z2010012286/Robot_car/models_v2/X3PI_3D_20220615175044.step

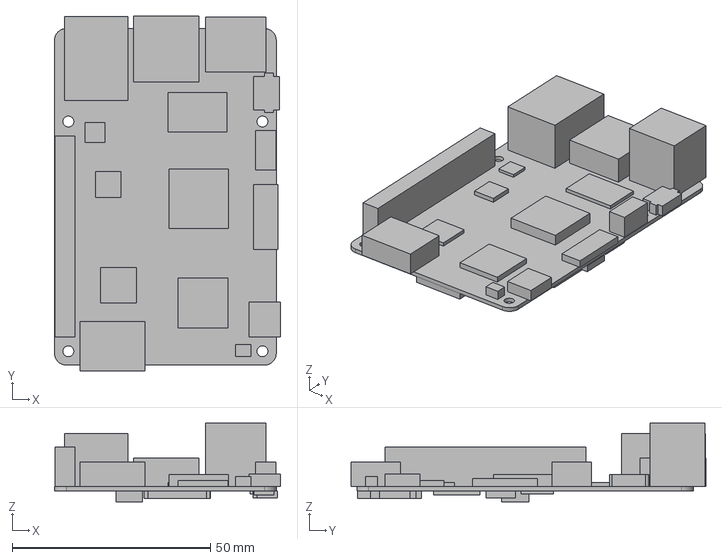
[picture p12: CAD file, 2022-10-31]
models_v2/X3PI_3D_20220615175044.step
57.1 x 89.6 x 19.9 mm
