z2010012286/Robot_car/models_v2/motor.SLDPRT

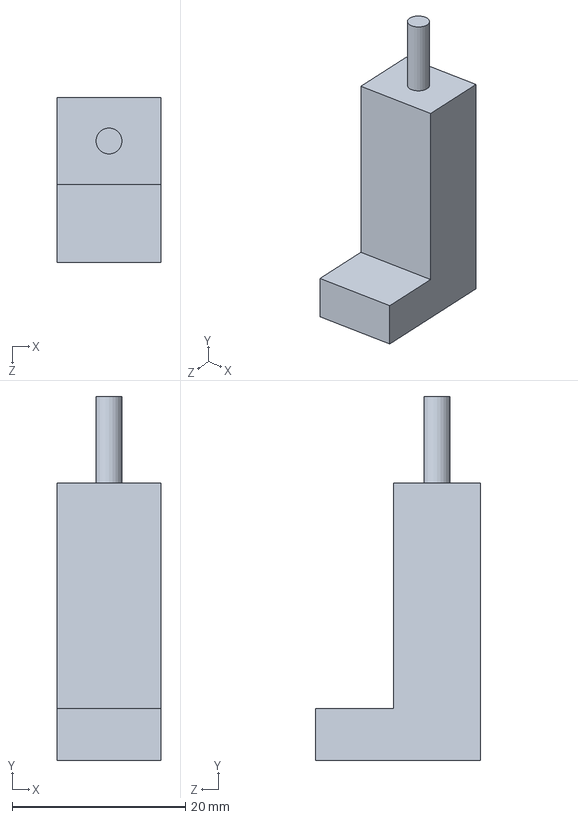
[picture p13: CAD file, 2022-10-31]
models_v2/motor.SLDPRT
12.0 x 42.0 x 19.0 mm
