z2010012286/Robot_car/models_v2/battery.SLDPRT

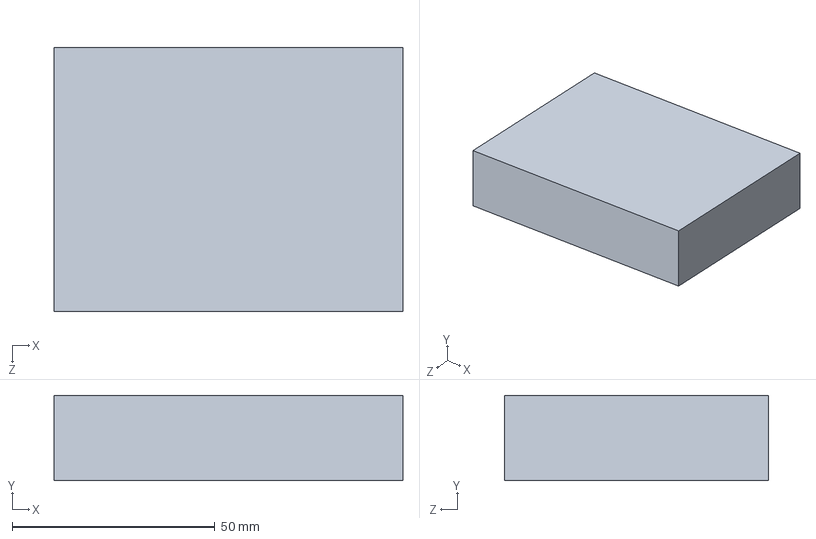
[picture p14: CAD file, 2022-10-31]
models_v2/battery.SLDPRT
86.0 x 21.0 x 65.0 mm
