z2010012286/Robot_car/codes/reconfig_code/unit_test/unit_test_micro_ros/test/micro_ros_debug.txt

[1669990941.373159] debug    | SerialAgentLinux.cpp | recv_message             | [==>> SER <<==]        | client_key: 0x3D3296CC, len: 20, data: 
0000: 81 01 0F 00 03 01 04 00 00 24 00 05 03 01 04 00 00 25 00 03
[1669990941.373207] debug    | ProxyClient.cpp    | delete_object_unlock     | object deleted         | client_key: 0x3D3296CC, object_id: 0x0000
[1669990941.373290] debug    | SerialAgentLinux.cpp | send_message             | [** <<SER>> **]        | client_key: 0x3D3296CC, len: 14, data: 
0000: 81 01 00 00 05 01 06 00 00 23 00 02 00 00
[1669990941.373598] debug    | ProxyClient.cpp    | delete_object_unlock     | object deleted         | client_key: 0x3D3296CC, object_id: 0x0000
[1669990941.373628] debug    | ProxyClient.cpp    | delete_object_unlock     | object deleted         | client_key: 0x3D3296CC, object_id: 0x0000
[1669990941.373599] debug    | SerialAgentLinux.cpp | recv_message             | [==>> SER <<==]        | client_key: 0x3D3296CC, len: 12, data: 
0000: 81 01 10 00 03 01 04 00 00 26 00 12
[1669990941.373666] debug    | SerialAgentLinux.cpp | recv_message             | [==>> SER <<==]        | client_key: 0x3D3296CC, len: 20, data: 
0000: 81 01 11 00 03 01 04 00 00 27 00 15 03 01 04 00 00 28 00 13
[1669990941.373682] debug    | SerialAgentLinux.cpp | recv_message             | [==>> SER <<==]        | client_key: 0x3D3296CC, len: 24, data: 
0000: 81 01 12 00 08 01 10 00 00 29 00 06 00 00 00 01 00 00 00 00 00 00 00 00
[1669990941.373686] debug    | SerialAgentLinux.cpp | send_message             | [** <<SER>> **]        | client_key: 0x3D3296CC, len: 14, data: 
0000: 81 01 01 00 05 01 06 00 00 24 00 05 00 00
[1669990941.373757] debug    | SerialAgentLinux.cpp | send_message             | [** <<SER>> **]        | client_key: 0x3D3296CC, len: 14, data: 
0000: 81 01 02 00 05 01 06 00 00 25 00 03 00 00
[1669990941.373690] debug    | ProxyClient.cpp    | delete_object_unlock     | object deleted         | client_key: 0x3D3296CC, object_id: 0x0001
[1669990941.373817] debug    | SerialAgentLinux.cpp | send_message             | [** <<SER>> **]        | client_key: 0x3D3296CC, len: 14, data: 
0000: 81 01 03 00 05 01 06 00 00 26 00 12 00 00
[1669990941.373908] debug    | ProxyClient.cpp    | delete_object_unlock     | object deleted         | client_key: 0x3D3296CC, object_id: 0x0001
[1669990941.373926] debug    | ProxyClient.cpp    | delete_object_unlock     | object deleted         | client_key: 0x3D3296CC, object_id: 0x0001
[1669990941.373979] debug    | SerialAgentLinux.cpp | send_message             | [** <<SER>> **]        | client_key: 0x3D3296CC, len: 14, data: 
0000: 81 01 04 00 05 01 06 00 00 27 00 15 00 00
[1669990941.374041] debug    | SerialAgentLinux.cpp | send_message             | [** <<SER>> **]        | client_key: 0x3D3296CC, len: 14, data: 
0000: 81 01 05 00 05 01 06 00 00 28 00 13 00 00
[1669990941.374121] debug    | SerialAgentLinux.cpp | recv_message             | [==>> SER <<==]        | client_key: 0x3D3296CC, len: 12, data: 
0000: 81 01 13 00 03 01 04 00 00 2A 00 22
[1669990941.374331] debug    | SerialAgentLinux.cpp | recv_message             | [==>> SER <<==]        | client_key: 0x3D3296CC, len: 20, data: 
0000: 81 01 14 00 03 01 04 00 00 2B 00 06 03 01 04 00 00 2C 00 04
[1669990941.374347] debug    | SerialAgentLinux.cpp | recv_message             | [==>> SER <<==]        | client_key: 0x3D3296CC, len: 12, data: 
0000: 81 01 15 00 03 01 04 00 00 2D 00 01
[1669990941.374642] debug    | SerialAgentLinux.cpp | recv_message             | [==>> SER <<==]        | client_key: 0x3D3296CC, len: 12, data: 
0000: 81 00 00 00 03 01 04 00 00 02 FF FE
[1669990941.441336] debug    | SerialAgentLinux.cpp | recv_message             | [==>> SER <<==]        | client_key: 0x3D3296CC, len: 16, data: 
0000: 80 00 00 00 02 01 08 00 00 0A FF FD 02 00 00 00
[1669990941.465860] debug    | ProxyClient.cpp    | delete_object_unlock     | object deleted         | client_key: 0x3D3296CC, object_id: 0x0002
[1669990941.465945] debug    | SerialAgentLinux.cpp | send_message             | [** <<SER>> **]        | client_key: 0x3D3296CC, len: 14, data: 
0000: 81 01 06 00 05 01 06 00 00 2A 00 22 00 00
[1669990941.566336] debug    | ProxyClient.cpp    | delete_object_unlock     | object deleted         | client_key: 0x3D3296CC, object_id: 0x0000
[1669990941.566383] debug    | ProxyClient.cpp    | delete_object_unlock     | object deleted         | client_key: 0x3D3296CC, object_id: 0x0000
[1669990941.566455] debug    | SerialAgentLinux.cpp | send_message             | [** <<SER>> **]        | client_key: 0x3D3296CC, len: 14, data: 
0000: 81 01 07 00 05 01 06 00 00 2B 00 06 00 00
[1669990941.566472] debug    | SerialAgentLinux.cpp | send_message             | [** <<SER>> **]        | client_key: 0x3D3296CC, len: 14, data: 
0000: 81 01 08 00 05 01 06 00 00 2C 00 04 00 00
[1669990941.569401] debug    | ProxyClient.cpp    | delete_object_unlock     | object deleted         | client_key: 0x3D3296CC, object_id: 0x0000
[1669990941.569477] info     | Root.cpp           | delete_client            | delete                 | client_key: 0x3D3296CC
[1669990941.569487] info     | SessionManager.hpp | destroy_session          | session closed         | client_key: 0x3D3296CC, address: 0
[1669990942.097232] info     | Root.cpp           | create_client            | create                 | client_key: 0x6A81087C, session_id: 0x81
[1669990942.097269] info     | SessionManager.hpp | establish_session        | session established    | client_key: 0x6A81087C, address: 0
[1669990942.097346] debug    | SerialAgentLinux.cpp | send_message             | [** <<SER>> **]        | client_key: 0x6A81087C, len: 19, data: 
0000: 81 00 00 00 04 01 0B 00 00 00 58 52 43 45 01 00 01 0F 00
[1669990942.101663] debug    | SerialAgentLinux.cpp | recv_message             | [==>> SER <<==]        | client_key: 0x6A81087C, len: 48, data: 
0000: 81 80 00 00 01 07 28 00 00 0A 00 01 01 03 00 00 1A 00 00 00 00 01 0D 80 12 00 00 00 74 69 61 6E
0020: 63 69 5F 72 6F 62 6F 74 5F 6E 6F 64 65 00 00 00
[1669990942.110478] info     | ProxyClient.cpp    | create_participant       | participant created    | client_key: 0x6A81087C, participant_id: 0x000(1)
[1669990942.110544] debug    | SerialAgentLinux.cpp | send_message             | [** <<SER>> **]        | client_key: 0x6A81087C, len: 14, data: 
0000: 81 80 00 00 05 01 06 00 00 0A 00 01 00 00
[1669990942.110566] debug    | SerialAgentLinux.cpp | send_message             | [** <<SER>> **]        | client_key: 0x6A81087C, len: 13, data: 
0000: 81 00 00 00 0A 01 05 00 01 00 00 00 80
[1669990942.114766] debug    | SerialAgentLinux.cpp | recv_message             | [==>> SER <<==]        | client_key: 0x6A81087C, len: 13, data: 
0000: 81 00 00 00 0A 01 05 00 01 00 00 00 80
[1669990942.118054] debug    | SerialAgentLinux.cpp | recv_message             | [==>> SER <<==]        | client_key: 0x6A81087C, len: 88, data: 
0000: 81 80 01 00 01 07 4D 00 00 0B 00 02 02 03 00 00 3F 00 00 00 13 00 00 00 72 74 2F 6F 64 6F 6D 2F
0020: 75 6E 66 69 6C 74 65 72 65 64 00 00 01 00 00 00 1F 00 00 00 6E 61 76 5F 6D 73 67 73 3A 3A 6D 73
0040: 67 3A 3A 64 64 73 5F 3A 3A 4F 64 6F 6D 65 74 72 79 5F 00 00 01 00 00 00
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
[1669990943.109060] debug    | ProxyClient.cpp    | delete_object_unlock     | object deleted         | client_key: 0x6A81087C, object_id: 0x0000
[1669990943.109068] debug    | ProxyClient.cpp    | delete_object_unlock     | object deleted         | client_key: 0x6A81087C, object_id: 0x0001
[1669990943.109170] debug    | ProxyClient.cpp    | delete_object_unlock     | object deleted         | client_key: 0x6A81087C, object_id: 0x0001
[1669990943.109190] debug    | ProxyClient.cpp    | delete_object_unlock     | object deleted         | client_key: 0x6A81087C, object_id: 0x0001
[1669990943.109276] debug    | SerialAgentLinux.cpp | send_message             | [** <<SER>> **]        | client_key: 0x6A81087C, len: 14, data: 
0000: 81 01 01 00 05 01 06 00 00 50 00 05 00 00
[1669990943.109339] debug    | SerialAgentLinux.cpp | send_message             | [** <<SER>> **]        | client_key: 0x6A81087C, len: 14, data: 
0000: 81 01 02 00 05 01 06 00 00 51 00 03 00 00
[1669990943.109343] debug    | SerialAgentLinux.cpp | send_message             | [** <<SER>> **]        | client_key: 0x6A81087C, len: 14, data: 
0000: 81 01 03 00 05 01 06 00 00 52 00 12 00 00
[1669990943.109347] debug    | SerialAgentLinux.cpp | send_message             | [** <<SER>> **]        | client_key: 0x6A81087C, len: 14, data: 
0000: 81 01 04 00 05 01 06 00 00 53 00 15 00 00
[1669990943.109351] debug    | SerialAgentLinux.cpp | send_message             | [** <<SER>> **]        | client_key: 0x6A81087C, len: 14, data: 
0000: 81 01 05 00 05 01 06 00 00 54 00 13 00 00
[1669990943.109319] debug    | SerialAgentLinux.cpp | recv_message             | [==>> SER <<==]        | client_key: 0x6A81087C, len: 20, data: 
0000: 81 01 40 00 03 01 04 00 00 57 00 06 03 01 04 00 00 58 00 04
[1669990943.109407] debug    | SerialAgentLinux.cpp | recv_message             | [==>> SER <<==]        | client_key: 0x6A81087C, len: 12, data: 
0000: 81 01 41 00 03 01 04 00 00 59 00 01
[1669990943.109419] debug    | SerialAgentLinux.cpp | recv_message             | [==>> SER <<==]        | client_key: 0x6A81087C, len: 12, data: 
0000: 81 00 00 00 03 01 04 00 00 02 FF FE
[1669990943.121271] debug    | SerialAgentLinux.cpp | recv_message             | [==>> SER <<==]        | client_key: 0x6A81087C, len: 16, data: 
0000: 80 00 00 00 02 01 08 00 00 0A FF FD 02 00 00 00
[1669990943.169467] debug    | ProxyClient.cpp    | delete_object_unlock     | object deleted         | client_key: 0x6A81087C, object_id: 0x0002
[1669990943.169548] debug    | SerialAgentLinux.cpp | send_message             | [** <<SER>> **]        | client_key: 0x6A81087C, len: 14, data: 
0000: 81 01 06 00 05 01 06 00 00 56 00 22 00 00
[1669990943.270036] debug    | ProxyClient.cpp    | delete_object_unlock     | object deleted         | client_key: 0x6A81087C, object_id: 0x0000
[1669990943.270118] debug    | ProxyClient.cpp    | delete_object_unlock     | object deleted         | client_key: 0x6A81087C, object_id: 0x0000
[1669990943.270188] debug    | SerialAgentLinux.cpp | send_message             | [** <<SER>> **]        | client_key: 0x6A81087C, len: 14, data: 
0000: 81 01 07 00 05 01 06 00 00 57 00 06 00 00
[1669990943.270210] debug    | SerialAgentLinux.cpp | send_message             | [** <<SER>> **]        | client_key: 0x6A81087C, len: 14, data: 
0000: 81 01 08 00 05 01 06 00 00 58 00 04 00 00
[1669990943.273466] debug    | ProxyClient.cpp    | delete_object_unlock     | object deleted         | client_key: 0x6A81087C, object_id: 0x0000
[1669990943.273542] info     | Root.cpp           | delete_client            | delete                 | client_key: 0x6A81087C
[1669990943.273555] info     | SessionManager.hpp | destroy_session          | session closed         | client_key: 0x6A81087C, address: 0
[1669990943.801147] info     | Root.cpp           | create_client            | create                 | client_key: 0x2B858398, session_id: 0x81
[1669990943.801186] info     | SessionManager.hpp | establish_session        | session established    | client_key: 0x2B858398, address: 0
[1669990943.801241] debug    | SerialAgentLinux.cpp | send_message             | [** <<SER>> **]        | client_key: 0x2B858398, len: 19, data: 
0000: 81 00 00 00 04 01 0B 00 00 00 58 52 43 45 01 00 01 0F 00
[1669990943.805449] debug    | SerialAgentLinux.cpp | recv_message             | [==>> SER <<==]        | client_key: 0x2B858398, len: 48, data: 
0000: 81 80 00 00 01 07 28 00 00 0A 00 01 01 03 00 00 1A 00 00 00 00 01 00 00 12 00 00 00 74 69 61 6E
0020: 63 69 5F 72 6F 62 6F 74 5F 6E 6F 64 65 00 00 00
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
[1669990944.190704] debug    | SerialAgentLinux.cpp | send_message             | [** <<SER>> **]        | client_key: 0x2B858398, len: 14, data: 
0000: 81 01 03 00 05 01 06 00 00 26 00 12 00 00
[1669990944.190837] debug    | ProxyClient.cpp    | delete_object_unlock     | object deleted         | client_key: 0x2B858398, object_id: 0x0001
[1669990944.190868] debug    | ProxyClient.cpp    | delete_object_unlock     | object deleted         | client_key: 0x2B858398, object_id: 0x0001
[1669990944.190926] debug    | SerialAgentLinux.cpp | send_message             | [** <<SER>> **]        | client_key: 0x2B858398, len: 14, data: 
0000: 81 01 04 00 05 01 06 00 00 27 00 15 00 00
[1669990944.190950] debug    | SerialAgentLinux.cpp | send_message             | [** <<SER>> **]        | client_key: 0x2B858398, len: 14, data: 
0000: 81 01 05 00 05 01 06 00 00 28 00 13 00 00
[1669990944.193062] debug    | SerialAgentLinux.cpp | recv_message             | [==>> SER <<==]        | client_key: 0x2B858398, len: 12, data: 
0000: 81 01 13 00 03 01 04 00 00 2A 00 22
[1669990944.194585] debug    | SerialAgentLinux.cpp | recv_message             | [==>> SER <<==]        | client_key: 0x2B858398, len: 20, data: 
0000: 81 01 14 00 03 01 04 00 00 2B 00 06 03 01 04 00 00 2C 00 04
[1669990944.194591] debug    | SerialAgentLinux.cpp | recv_message             | [==>> SER <<==]        | client_key: 0x2B858398, len: 12, data: 
0000: 81 01 15 00 03 01 04 00 00 2D 00 01
[1669990944.194597] debug    | SerialAgentLinux.cpp | recv_message             | [==>> SER <<==]        | client_key: 0x2B858398, len: 12, data: 
0000: 81 00 00 00 03 01 04 00 00 02 FF FE
[1669990944.282007] debug    | ProxyClient.cpp    | delete_object_unlock     | object deleted         | client_key: 0x2B858398, object_id: 0x0002
[1669990944.282204] debug    | SerialAgentLinux.cpp | send_message             | [** <<SER>> **]        | client_key: 0x2B858398, len: 14, data: 
0000: 81 01 06 00 05 01 06 00 00 2A 00 22 00 00
[1669990944.282452] debug    | ProxyClient.cpp    | delete_object_unlock     | object deleted         | client_key: 0x2B858398, object_id: 0x0000
[1669990944.282487] debug    | ProxyClient.cpp    | delete_object_unlock     | object deleted         | client_key: 0x2B858398, object_id: 0x0000
[1669990944.282689] debug    | SerialAgentLinux.cpp | send_message             | [** <<SER>> **]        | client_key: 0x2B858398, len: 14, data: 
0000: 81 01 07 00 05 01 06 00 00 2B 00 06 00 00
[1669990944.282705] debug    | SerialAgentLinux.cpp | send_message             | [** <<SER>> **]        | client_key: 0x2B858398, len: 14, data: 
0000: 81 01 08 00 05 01 06 00 00 2C 00 04 00 00
[1669990944.289593] debug    | ProxyClient.cpp    | delete_object_unlock     | object deleted         | client_key: 0x2B858398, object_id: 0x0000
[1669990944.289670] info     | Root.cpp           | delete_client            | delete                 | client_key: 0x2B858398
[1669990944.289686] info     | SessionManager.hpp | destroy_session          | session closed         | client_key: 0x2B858398, address: 0
[1669990944.317212] info     | Root.cpp           | create_client            | create                 | client_key: 0x6B437B96, session_id: 0x81
[1669990944.317246] info     | SessionManager.hpp | establish_session        | session established    | client_key: 0x6B437B96, address: 0
[1669990944.317301] debug    | SerialAgentLinux.cpp | send_message             | [** <<SER>> **]        | client_key: 0x6B437B96, len: 19, data: 
0000: 81 00 00 00 04 01 0B 00 00 00 58 52 43 45 01 00 01 0F 00
[1669990944.321505] debug    | SerialAgentLinux.cpp | recv_message             | [==>> SER <<==]        | client_key: 0x6B437B96, len: 48, data: 
0000: 81 80 00 00 01 07 28 00 00 0A 00 01 01 03 00 00 1A 00 00 00 00 01 3F B3 12 00 00 00 74 69 61 6E
0020: 63 69 5F 72 6F 62 6F 74 5F 6E 6F 64 65 00 00 00
[1669990944.330592] info     | ProxyClient.cpp    | create_participant       | participant created    | client_key: 0x6B437B96, participant_id: 0x000(1)
[1669990944.330687] debug    | SerialAgentLinux.cpp | send_message             | [** <<SER>> **]        | client_key: 0x6B437B96, len: 14, data: 
0000: 81 80 00 00 05 01 06 00 00 0A 00 01 00 00
[1669990944.330706] debug    | SerialAgentLinux.cpp | send_message             | [** <<SER>> **]        | client_key: 0x6B437B96, len: 13, data: 
0000: 81 00 00 00 0A 01 05 00 01 00 00 00 80
[1669990944.334440] debug    | SerialAgentLinux.cpp | recv_message             | [==>> SER <<==]        | client_key: 0x6B437B96, len: 13, data: 
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
0000: 81 01 1F 00 03 01 04 00 00 35 00 12
[1669990944.925240] debug    | SerialAgentLinux.cpp | recv_message             | [==>> SER <<==]        | client_key: 0x6B437B96, len: 20, data: 
0000: 81 01 20 00 03 01 04 00 00 36 00 15 03 01 04 00 00 37 00 13
[1669990944.925216] debug    | ProxyClient.cpp    | delete_object_unlock     | object deleted         | client_key: 0x6B437B96, object_id: 0x0000
[1669990944.925351] debug    | SerialAgentLinux.cpp | send_message             | [** <<SER>> **]        | client_key: 0x6B437B96, len: 14, data: 
0000: 81 01 00 00 05 01 06 00 00 32 00 02 00 00
[1669990944.925706] debug    | SerialAgentLinux.cpp | recv_message             | [==>> SER <<==]        | client_key: 0x6B437B96, len: 24, data: 
0000: 81 01 21 00 08 01 10 00 00 38 00 06 00 00 00 01 00 00 00 00 00 00 00 00
[1669990944.925849] debug    | SerialAgentLinux.cpp | recv_message             | [==>> SER <<==]        | client_key: 0x6B437B96, len: 12, data: 
0000: 81 01 22 00 03 01 04 00 00 39 00 22
[1669990944.925822] debug    | ProxyClient.cpp    | delete_object_unlock     | object deleted         | client_key: 0x6B437B96, object_id: 0x0000
[1669990944.925894] debug    | ProxyClient.cpp    | delete_object_unlock     | object deleted         | client_key: 0x6B437B96, object_id: 0x0000
[1669990944.925903] debug    | ProxyClient.cpp    | delete_object_unlock     | object deleted         | client_key: 0x6B437B96, object_id: 0x0001
[1669990944.925954] debug    | SerialAgentLinux.cpp | send_message             | [** <<SER>> **]        | client_key: 0x6B437B96, len: 14, data: 
0000: 81 01 01 00 05 01 06 00 00 33 00 05 00 00
[1669990944.925991] debug    | SerialAgentLinux.cpp | send_message             | [** <<SER>> **]        | client_key: 0x6B437B96, len: 14, data: 
0000: 81 01 02 00 05 01 06 00 00 34 00 03 00 00
[1669990944.925995] debug    | SerialAgentLinux.cpp | send_message             | [** <<SER>> **]        | client_key: 0x6B437B96, len: 14, data: 
0000: 81 01 03 00 05 01 06 00 00 35 00 12 00 00
[1669990944.926247] debug    | ProxyClient.cpp    | delete_object_unlock     | object deleted         | client_key: 0x6B437B96, object_id: 0x0001
[1669990944.926276] debug    | ProxyClient.cpp    | delete_object_unlock     | object deleted         | client_key: 0x6B437B96, object_id: 0x0001
[1669990944.926292] debug    | SerialAgentLinux.cpp | recv_message             | [==>> SER <<==]        | client_key: 0x6B437B96, len: 20, data: 
0000: 81 01 23 00 03 01 04 00 00 3A 00 06 03 01 04 00 00 3B 00 04
[1669990944.926304] debug    | SerialAgentLinux.cpp | recv_message             | [==>> SER <<==]        | client_key: 0x6B437B96, len: 12, data: 
0000: 81 01 24 00 03 01 04 00 00 3C 00 01
[1669990944.926310] debug    | SerialAgentLinux.cpp | send_message             | [** <<SER>> **]        | client_key: 0x6B437B96, len: 14, data: 
0000: 81 01 04 00 05 01 06 00 00 36 00 15 00 00
[1669990944.926334] debug    | SerialAgentLinux.cpp | send_message             | [** <<SER>> **]        | client_key: 0x6B437B96, len: 14, data: 
0000: 81 01 05 00 05 01 06 00 00 37 00 13 00 00
[1669990944.926649] debug    | SerialAgentLinux.cpp | recv_message             | [==>> SER <<==]        | client_key: 0x6B437B96, len: 12, data: 
0000: 81 00 00 00 03 01 04 00 00 02 FF FE
[1669990944.937858] debug    | SerialAgentLinux.cpp | recv_message             | [==>> SER <<==]        | client_key: 0x6B437B96, len: 16, data: 
0000: 80 00 00 00 02 01 08 00 00 0A FF FD 02 00 00 00
[1669990945.010606] debug    | ProxyClient.cpp    | delete_object_unlock     | object deleted         | client_key: 0x6B437B96, object_id: 0x0002
[1669990945.010720] debug    | SerialAgentLinux.cpp | send_message             | [** <<SER>> **]        | client_key: 0x6B437B96, len: 14, data: 
0000: 81 01 06 00 05 01 06 00 00 39 00 22 00 00
[1669990945.113115] debug    | ProxyClient.cpp    | delete_object_unlock     | object deleted         | client_key: 0x6B437B96, object_id: 0x0000
[1669990945.113166] debug    | ProxyClient.cpp    | delete_object_unlock     | object deleted         | client_key: 0x6B437B96, object_id: 0x0000
[1669990945.113214] debug    | SerialAgentLinux.cpp | send_message             | [** <<SER>> **]        | client_key: 0x6B437B96, len: 14, data: 
0000: 81 01 07 00 05 01 06 00 00 3A 00 06 00 00
[1669990945.113231] debug    | SerialAgentLinux.cpp | send_message             | [** <<SER>> **]        | client_key: 0x6B437B96, len: 14, data: 
0000: 81 01 08 00 05 01 06 00 00 3B 00 04 00 00
[1669990945.114383] debug    | ProxyClient.cpp    | delete_object_unlock     | object deleted         | client_key: 0x6B437B96, object_id: 0x0000
[1669990945.114452] info     | Root.cpp           | delete_client            | delete                 | client_key: 0x6B437B96
[1669990945.114474] info     | SessionManager.hpp | destroy_session          | session closed         | client_key: 0x6B437B96, address: 0
[1669990945.641209] info     | Root.cpp           | create_client            | create                 | client_key: 0x4D7A2CF8, session_id: 0x81
[1669990945.641248] info     | SessionManager.hpp | establish_session        | session established    | client_key: 0x4D7A2CF8, address: 0
[1669990945.641304] debug    | SerialAgentLinux.cpp | send_message             | [** <<SER>> **]        | client_key: 0x4D7A2CF8, len: 19, data: 
0000: 81 00 00 00 04 01 0B 00 00 00 58 52 43 45 01 00 01 0F 00
[1669990945.645369] debug    | SerialAgentLinux.cpp | recv_message             | [==>> SER <<==]        | client_key: 0x4D7A2CF8, len: 48, data: 
0000: 81 80 00 00 01 07 28 00 00 0A 00 01 01 03 00 00 1A 00 00 00 00 01 00 00 12 00 00 00 74 69 61 6E
0020: 63 69 5F 72 6F 62 6F 74 5F 6E 6F 64 65 00 00 00
[1669990945.649835] info     | ProxyClient.cpp    | create_participant       | participant created    | client_key: 0x4D7A2CF8, participant_id: 0x000(1)
[1669990945.650248] debug    | SerialAgentLinux.cpp | send_message             | [** <<SER>> **]        | client_key: 0x4D7A2CF8, len: 14, data: 
0000: 81 80 00 00 05 01 06 00 00 0A 00 01 00 00
[1669990945.650296] debug    | SerialAgentLinux.cpp | send_message             | [** <<SER>> **]        | client_key: 0x4D7A2CF8, len: 13, data: 
0000: 81 00 00 00 0A 01 05 00 01 00 00 00 80
[1669990945.653221] debug    | SerialAgentLinux.cpp | recv_message             | [==>> SER <<==]        | client_key: 0x4D7A2CF8, len: 13, data: 
0000: 81 00 00 00 0A 01 05 00 01 00 00 00 80
[1669990945.658512] debug    | SerialAgentLinux.cpp | recv_message             | [==>> SER <<==]        | client_key: 0x4D7A2CF8, len: 88, data: 
0000: 81 80 01 00 01 07 4D 00 00 0B 00 02 02 03 00 00 3F 00 00 00 13 00 00 00 72 74 2F 6F 64 6F 6D 2F
0020: 75 6E 66 69 6C 74 65 72 65 64 00 00 01 00 00 00 1F 00 00 00 6E 61 76 5F 6D 73 67 73 3A 3A 6D 73
0040: 67 3A 3A 64 64 73 5F 3A 3A 4F 64 6F 6D 65 74 72 79 5F 00 00 01 00 00 00
[1669990945.658594] info     | ProxyClient.cpp    | create_topic             | topic created          | client_key: 0x4D7A2CF8, topic_id: 0x000(2), participant_id: 0x000(1)
[1669990945.658656] debug    | SerialAgentLinux.cpp | send_message             | [** <<SER>> **]        | client_key: 0x4D7A2CF8, len: 14, data: 
0000: 81 80 01 00 05 01 06 00 00 0B 00 02 00 00
[1669990945.658675] debug    | SerialAgentLinux.cpp | send_message             | [** <<SER>> **]        | client_key: 0x4D7A2CF8, len: 13, data: 
0000: 81 00 00 00 0A 01 05 00 02 00 00 00 80
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
0000: 81 01 02 00 05 01 06 00 00 51 00 03 00 00
[1669990946.662829] debug    | SerialAgentLinux.cpp | send_message             | [** <<SER>> **]        | client_key: 0x4D7A2CF8, len: 14, data: 
0000: 81 01 03 00 05 01 06 00 00 52 00 12 00 00
[1669990946.662792] debug    | SerialAgentLinux.cpp | recv_message             | [==>> SER <<==]        | client_key: 0x4D7A2CF8, len: 12, data: 
0000: 81 01 3F 00 03 01 04 00 00 56 00 22
[1669990946.665158] debug    | SerialAgentLinux.cpp | recv_message             | [==>> SER <<==]        | client_key: 0x4D7A2CF8, len: 20, data: 
0000: 81 01 40 00 03 01 04 00 00 57 00 06 03 01 04 00 00 58 00 04
[1669990946.665165] debug    | SerialAgentLinux.cpp | recv_message             | [==>> SER <<==]        | client_key: 0x4D7A2CF8, len: 12, data: 
0000: 81 01 41 00 03 01 04 00 00 59 00 01
[1669990946.665171] debug    | SerialAgentLinux.cpp | recv_message             | [==>> SER <<==]        | client_key: 0x4D7A2CF8, len: 12, data: 
0000: 81 00 00 00 03 01 04 00 00 02 FF FE
[1669990946.665257] debug    | ProxyClient.cpp    | delete_object_unlock     | object deleted         | client_key: 0x4D7A2CF8, object_id: 0x0001
[1669990946.665302] debug    | ProxyClient.cpp    | delete_object_unlock     | object deleted         | client_key: 0x4D7A2CF8, object_id: 0x0001
[1669990946.665329] debug    | SerialAgentLinux.cpp | send_message             | [** <<SER>> **]        | client_key: 0x4D7A2CF8, len: 14, data: 
0000: 81 01 04 00 05 01 06 00 00 53 00 15 00 00
[1669990946.665338] debug    | SerialAgentLinux.cpp | send_message             | [** <<SER>> **]        | client_key: 0x4D7A2CF8, len: 14, data: 
0000: 81 01 05 00 05 01 06 00 00 54 00 13 00 00
[1669990946.674749] debug    | SerialAgentLinux.cpp | recv_message             | [==>> SER <<==]        | client_key: 0x4D7A2CF8, len: 16, data: 
0000: 80 00 00 00 02 01 08 00 00 0A FF FD 02 00 00 00
[1669990946.722300] debug    | ProxyClient.cpp    | delete_object_unlock     | object deleted         | client_key: 0x4D7A2CF8, object_id: 0x0002
[1669990946.722353] debug    | SerialAgentLinux.cpp | send_message             | [** <<SER>> **]        | client_key: 0x4D7A2CF8, len: 14, data: 
0000: 81 01 06 00 05 01 06 00 00 56 00 22 00 00
[1669990946.722775] debug    | ProxyClient.cpp    | delete_object_unlock     | object deleted         | client_key: 0x4D7A2CF8, object_id: 0x0000
[1669990946.722825] debug    | ProxyClient.cpp    | delete_object_unlock     | object deleted         | client_key: 0x4D7A2CF8, object_id: 0x0000
[1669990946.722907] debug    | SerialAgentLinux.cpp | send_message             | [** <<SER>> **]        | client_key: 0x4D7A2CF8, len: 14, data: 
0000: 81 01 07 00 05 01 06 00 00 57 00 06 00 00
[1669990946.722923] debug    | SerialAgentLinux.cpp | send_message             | [** <<SER>> **]        | client_key: 0x4D7A2CF8, len: 14, data: 
0000: 81 01 08 00 05 01 06 00 00 58 00 04 00 00
[1669990946.726190] debug    | ProxyClient.cpp    | delete_object_unlock     | object deleted         | client_key: 0x4D7A2CF8, object_id: 0x0000
[1669990946.726248] info     | Root.cpp           | delete_client            | delete                 | client_key: 0x4D7A2CF8
[1669990946.726258] info     | SessionManager.hpp | destroy_session          | session closed         | client_key: 0x4D7A2CF8, address: 0
[1669990946.745177] info     | Root.cpp           | create_client            | create                 | client_key: 0x78EBFE0E, session_id: 0x81
[1669990946.745207] info     | SessionManager.hpp | establish_session        | session established    | client_key: 0x78EBFE0E, address: 0
[1669990946.745283] debug    | SerialAgentLinux.cpp | send_message             | [** <<SER>> **]        | client_key: 0x78EBFE0E, len: 19, data: 
0000: 81 00 00 00 04 01 0B 00 00 00 58 52 43 45 01 00 01 0F 00
[1669990946.749362] debug    | SerialAgentLinux.cpp | recv_message             | [==>> SER <<==]        | client_key: 0x78EBFE0E, len: 48, data: 
0000: 81 80 00 00 01 07 28 00 00 0A 00 01 01 03 00 00 1A 00 00 00 00 01 00 00 12 00 00 00 74 69 61 6E
0020: 63 69 5F 72 6F 62 6F 74 5F 6E 6F 64 65 00 00 00
[1669990946.754015] info     | ProxyClient.cpp    | create_participant       | participant created    | client_key: 0x78EBFE0E, participant_id: 0x000(1)
[1669990946.754067] debug    | SerialAgentLinux.cpp | send_message             | [** <<SER>> **]        | client_key: 0x78EBFE0E, len: 14, data: 
0000: 81 80 00 00 05 01 06 00 00 0A 00 01 00 00
[1669990946.754084] debug    | SerialAgentLinux.cpp | send_message             | [** <<SER>> **]        | client_key: 0x78EBFE0E, len: 13, data: 
0000: 81 00 00 00 0A 01 05 00 01 00 00 00 80
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
0000: 81 01 03 00 03 01 04 00 00 18 00 02
[1669990946.966976] debug    | SerialAgentLinux.cpp | recv_message             | [==>> SER <<==]        | client_key: 0x78EBFE0E, len: 20, data: 
0000: 81 01 04 00 03 01 04 00 00 19 00 05 03 01 04 00 00 1A 00 03
[1669990946.966983] debug    | SerialAgentLinux.cpp | recv_message             | [==>> SER <<==]        | client_key: 0x78EBFE0E, len: 12, data: 
0000: 81 01 05 00 03 01 04 00 00 1B 00 12
[1669990946.966990] debug    | SerialAgentLinux.cpp | recv_message             | [==>> SER <<==]        | client_key: 0x78EBFE0E, len: 20, data: 
0000: 81 01 06 00 03 01 04 00 00 1C 00 15 03 01 04 00 00 1D 00 13
[1669990946.967006] debug    | SerialAgentLinux.cpp | recv_message             | [==>> SER <<==]        | client_key: 0x78EBFE0E, len: 24, data: 
0000: 81 01 07 00 08 01 10 00 00 1E 00 06 00 00 00 01 00 00 00 00 00 00 00 00
[1669990946.967013] debug    | SerialAgentLinux.cpp | recv_message             | [==>> SER <<==]        | client_key: 0x78EBFE0E, len: 12, data: 
0000: 81 01 08 00 03 01 04 00 00 1F 00 22
[1669990946.967019] debug    | SerialAgentLinux.cpp | recv_message             | [==>> SER <<==]        | client_key: 0x78EBFE0E, len: 20, data: 
0000: 81 01 09 00 03 01 04 00 00 20 00 06 03 01 04 00 00 21 00 04
[1669990946.967049] debug    | SerialAgentLinux.cpp | recv_message             | [==>> SER <<==]        | client_key: 0x78EBFE0E, len: 12, data: 
0000: 81 01 0A 00 03 01 04 00 00 22 00 01
[1669990946.967055] debug    | SerialAgentLinux.cpp | recv_message             | [==>> SER <<==]        | client_key: 0x78EBFE0E, len: 12, data: 
0000: 81 00 00 00 03 01 04 00 00 02 FF FE
[1669990946.969054] debug    | ProxyClient.cpp    | delete_object_unlock     | object deleted         | client_key: 0x78EBFE0E, object_id: 0x0000
[1669990946.969310] debug    | SerialAgentLinux.cpp | send_message             | [** <<SER>> **]        | client_key: 0x78EBFE0E, len: 14, data: 
0000: 81 01 00 00 05 01 06 00 00 18 00 02 00 00
[1669990946.969646] debug    | ProxyClient.cpp    | delete_object_unlock     | object deleted         | client_key: 0x78EBFE0E, object_id: 0x0000
[1669990946.969682] debug    | ProxyClient.cpp    | delete_object_unlock     | object deleted         | client_key: 0x78EBFE0E, object_id: 0x0000
[1669990946.969699] debug    | ProxyClient.cpp    | delete_object_unlock     | object deleted         | client_key: 0x78EBFE0E, object_id: 0x0001
[1669990946.969700] debug    | SerialAgentLinux.cpp | send_message             | [** <<SER>> **]        | client_key: 0x78EBFE0E, len: 14, data: 
0000: 81 01 01 00 05 01 06 00 00 19 00 05 00 00
[1669990946.969706] debug    | SerialAgentLinux.cpp | send_message             | [** <<SER>> **]        | client_key: 0x78EBFE0E, len: 14, data: 
0000: 81 01 02 00 05 01 06 00 00 1A 00 03 00 00
[1669990946.969710] debug    | SerialAgentLinux.cpp | send_message             | [** <<SER>> **]        | client_key: 0x78EBFE0E, len: 14, data: 
0000: 81 01 03 00 05 01 06 00 00 1B 00 12 00 00
[1669990946.970051] debug    | ProxyClient.cpp    | delete_object_unlock     | object deleted         | client_key: 0x78EBFE0E, object_id: 0x0001
[1669990946.970080] debug    | ProxyClient.cpp    | delete_object_unlock     | object deleted         | client_key: 0x78EBFE0E, object_id: 0x0001
[1669990946.970130] debug    | SerialAgentLinux.cpp | send_message             | [** <<SER>> **]        | client_key: 0x78EBFE0E, len: 14, data: 
0000: 81 01 04 00 05 01 06 00 00 1C 00 15 00 00
[1669990946.970144] debug    | SerialAgentLinux.cpp | send_message             | [** <<SER>> **]        | client_key: 0x78EBFE0E, len: 14, data: 
0000: 81 01 05 00 05 01 06 00 00 1D 00 13 00 00
[1669990947.017269] debug    | ProxyClient.cpp    | delete_object_unlock     | object deleted         | client_key: 0x78EBFE0E, object_id: 0x0002
[1669990947.021064] debug    | SerialAgentLinux.cpp | send_message             | [** <<SER>> **]        | client_key: 0x78EBFE0E, len: 14, data: 
0000: 81 01 06 00 05 01 06 00 00 1F 00 22 00 00
[1669990947.118002] debug    | ProxyClient.cpp    | delete_object_unlock     | object deleted         | client_key: 0x78EBFE0E, object_id: 0x0000
[1669990947.118057] debug    | ProxyClient.cpp    | delete_object_unlock     | object deleted         | client_key: 0x78EBFE0E, object_id: 0x0000
[1669990947.118096] debug    | SerialAgentLinux.cpp | send_message             | [** <<SER>> **]        | client_key: 0x78EBFE0E, len: 14, data: 
0000: 81 01 07 00 05 01 06 00 00 20 00 06 00 00
[1669990947.118112] debug    | SerialAgentLinux.cpp | send_message             | [** <<SER>> **]        | client_key: 0x78EBFE0E, len: 14, data: 
0000: 81 01 08 00 05 01 06 00 00 21 00 04 00 00
[1669990947.125165] debug    | ProxyClient.cpp    | delete_object_unlock     | object deleted         | client_key: 0x78EBFE0E, object_id: 0x0000
[1669990947.125337] info     | Root.cpp           | delete_client            | delete                 | client_key: 0x78EBFE0E
[1669990947.125359] info     | SessionManager.hpp | destroy_session          | session closed         | client_key: 0x78EBFE0E, address: 0
[1669990947.261120] info     | Root.cpp           | create_client            | create                 | client_key: 0x3AC7053F, session_id: 0x81
[1669990947.261151] info     | SessionManager.hpp | establish_session        | session established    | client_key: 0x3AC7053F, address: 0
[1669990947.261215] debug    | SerialAgentLinux.cpp | send_message             | [** <<SER>> **]        | client_key: 0x3AC7053F, len: 19, data: 
0000: 81 00 00 00 04 01 0B 00 00 00 58 52 43 45 01 00 01 0F 00
[1669990947.265350] debug    | SerialAgentLinux.cpp | recv_message             | [==>> SER <<==]        | client_key: 0x3AC7053F, len: 48, data: 
0000: 81 80 00 00 01 07 28 00 00 0A 00 01 01 03 00 00 1A 00 00 00 00 01 00 00 12 00 00 00 74 69 61 6E
0020: 63 69 5F 72 6F 62 6F 74 5F 6E 6F 64 65 00 00 00
[1669990947.273265] info     | ProxyClient.cpp    | create_participant       | participant created    | client_key: 0x3AC7053F, participant_id: 0x000(1)
[1669990947.273333] debug    | SerialAgentLinux.cpp | send_message             | [** <<SER>> **]        | client_key: 0x3AC7053F, len: 14, data: 
0000: 81 80 00 00 05 01 06 00 00 0A 00 01 00 00
[1669990947.273342] debug    | SerialAgentLinux.cpp | send_message             | [** <<SER>> **]        | client_key: 0x3AC7053F, len: 13, data: 
0000: 81 00 00 00 0A 01 05 00 01 00 00 00 80
[1669990947.278829] debug    | SerialAgentLinux.cpp | recv_message             | [==>> SER <<==]        | client_key: 0x3AC7053F, len: 13, data: 
0000: 81 00 00 00 0A 01 05 00 01 00 00 00 80
[1669990947.281190] debug    | SerialAgentLinux.cpp | recv_message             | [==>> SER <<==]        | client_key: 0x3AC7053F, len: 88, data: 
0000: 81 80 01 00 01 07 4D 00 00 0B 00 02 02 03 00 00 3F 00 00 00 13 00 00 00 72 74 2F 6F 64 6F 6D 2F
0020: 75 6E 66 69 6C 74 65 72 65 64 00 00 01 DB FB 3F 1F 00 00 00 6E 61 76 5F 6D 73 67 73 3A 3A 6D 73
0040: 67 3A 3A 64 64 73 5F 3A 3A 4F 64 6F 6D 65 74 72 79 5F 00 00 01 00 00 00
[1669990947.281295] info     | ProxyClient.cpp    | create_topic             | topic created          | client_key: 0x3AC7053F, topic_id: 0x000(2), participant_id: 0x000(1)
[1669990947.281364] debug    | SerialAgentLinux.cpp | send_message             | [** <<SER>> **]        | client_key: 0x3AC7053F, len: 14, data: 
0000: 81 80 01 00 05 01 06 00 00 0B 00 02 00 00
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
[1669990947.994028] debug    | ProxyClient.cpp    | delete_object_unlock     | object deleted         | client_key: 0x3AC7053F, object_id: 0x0000
[1669990947.994036] debug    | ProxyClient.cpp    | delete_object_unlock     | object deleted         | client_key: 0x3AC7053F, object_id: 0x0001
[1669990947.994218] debug    | SerialAgentLinux.cpp | send_message             | [** <<SER>> **]        | client_key: 0x3AC7053F, len: 14, data: 
0000: 81 01 01 00 05 01 06 00 00 33 00 05 00 00
[1669990947.994236] debug    | SerialAgentLinux.cpp | send_message             | [** <<SER>> **]        | client_key: 0x3AC7053F, len: 14, data: 
0000: 81 01 02 00 05 01 06 00 00 34 00 03 00 00
[1669990947.994240] debug    | SerialAgentLinux.cpp | send_message             | [** <<SER>> **]        | client_key: 0x3AC7053F, len: 14, data: 
0000: 81 01 03 00 05 01 06 00 00 35 00 12 00 00
[1669990947.994222] debug    | ProxyClient.cpp    | delete_object_unlock     | object deleted         | client_key: 0x3AC7053F, object_id: 0x0001
[1669990947.994362] debug    | ProxyClient.cpp    | delete_object_unlock     | object deleted         | client_key: 0x3AC7053F, object_id: 0x0001
[1669990947.994387] debug    | SerialAgentLinux.cpp | send_message             | [** <<SER>> **]        | client_key: 0x3AC7053F, len: 14, data: 
0000: 81 01 04 00 05 01 06 00 00 36 00 15 00 00
[1669990947.994399] debug    | SerialAgentLinux.cpp | send_message             | [** <<SER>> **]        | client_key: 0x3AC7053F, len: 14, data: 
0000: 81 01 05 00 05 01 06 00 00 37 00 13 00 00
[1669990948.037415] debug    | ProxyClient.cpp    | delete_object_unlock     | object deleted         | client_key: 0x3AC7053F, object_id: 0x0002
[1669990948.037534] debug    | SerialAgentLinux.cpp | send_message             | [** <<SER>> **]        | client_key: 0x3AC7053F, len: 14, data: 
0000: 81 01 06 00 05 01 06 00 00 39 00 22 00 00
[1669990948.038052] debug    | ProxyClient.cpp    | delete_object_unlock     | object deleted         | client_key: 0x3AC7053F, object_id: 0x0000
[1669990948.038087] debug    | ProxyClient.cpp    | delete_object_unlock     | object deleted         | client_key: 0x3AC7053F, object_id: 0x0000
[1669990948.038130] debug    | SerialAgentLinux.cpp | send_message             | [** <<SER>> **]        | client_key: 0x3AC7053F, len: 14, data: 
0000: 81 01 07 00 05 01 06 00 00 3A 00 06 00 00
[1669990948.038145] debug    | SerialAgentLinux.cpp | send_message             | [** <<SER>> **]        | client_key: 0x3AC7053F, len: 14, data: 
0000: 81 01 08 00 05 01 06 00 00 3B 00 04 00 00
[1669990948.045301] debug    | ProxyClient.cpp    | delete_object_unlock     | object deleted         | client_key: 0x3AC7053F, object_id: 0x0000
[1669990948.045424] info     | Root.cpp           | delete_client            | delete                 | client_key: 0x3AC7053F
[1669990948.045446] info     | SessionManager.hpp | destroy_session          | session closed         | client_key: 0x3AC7053F, address: 0
[1669990948.501137] info     | Root.cpp           | create_client            | create                 | client_key: 0x07DB5524, session_id: 0x81
[1669990948.501175] info     | SessionManager.hpp | establish_session        | session established    | client_key: 0x07DB5524, address: 0
[1669990948.501284] debug    | SerialAgentLinux.cpp | send_message             | [** <<SER>> **]        | client_key: 0x07DB5524, len: 19, data: 
0000: 81 00 00 00 04 01 0B 00 00 00 58 52 43 45 01 00 01 0F 00
[1669990948.505207] debug    | SerialAgentLinux.cpp | recv_message             | [==>> SER <<==]        | client_key: 0x07DB5524, len: 48, data: 
0000: 81 80 00 00 01 07 28 00 00 0A 00 01 01 03 00 00 1A 00 00 00 00 01 08 80 12 00 00 00 74 69 61 6E
0020: 63 69 5F 72 6F 62 6F 74 5F 6E 6F 64 65 00 00 00
[1669990948.507364] info     | ProxyClient.cpp    | create_participant       | participant created    | client_key: 0x07DB5524, participant_id: 0x000(1)
[1669990948.509691] debug    | SerialAgentLinux.cpp | send_message             | [** <<SER>> **]        | client_key: 0x07DB5524, len: 14, data: 
0000: 81 80 00 00 05 01 06 00 00 0A 00 01 00 00
[1669990948.509711] debug    | SerialAgentLinux.cpp | send_message             | [** <<SER>> **]        | client_key: 0x07DB5524, len: 13, data: 
0000: 81 00 00 00 0A 01 05 00 01 00 00 00 80
[1669990948.513766] debug    | SerialAgentLinux.cpp | recv_message             | [==>> SER <<==]        | client_key: 0x07DB5524, len: 13, data: 
0000: 81 00 00 00 0A 01 05 00 01 00 00 00 80
[1669990948.517118] debug    | SerialAgentLinux.cpp | recv_message             | [==>> SER <<==]        | client_key: 0x07DB5524, len: 88, data: 
0000: 81 80 01 00 01 07 4D 00 00 0B 00 02 02 03 00 00 3F 00 00 00 13 00 00 00 72 74 2F 6F 64 6F 6D 2F
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
0000: 81 01 00 00 05 01 06 00 00 23 00 02 00 00
[1669990948.881926] debug    | ProxyClient.cpp    | delete_object_unlock     | object deleted         | client_key: 0x07DB5524, object_id: 0x0000
[1669990948.882000] debug    | ProxyClient.cpp    | delete_object_unlock     | object deleted         | client_key: 0x07DB5524, object_id: 0x0000
[1669990948.882018] debug    | ProxyClient.cpp    | delete_object_unlock     | object deleted         | client_key: 0x07DB5524, object_id: 0x0001
[1669990948.882032] debug    | SerialAgentLinux.cpp | send_message             | [** <<SER>> **]        | client_key: 0x07DB5524, len: 14, data: 
0000: 81 01 01 00 05 01 06 00 00 24 00 05 00 00
[1669990948.882074] debug    | SerialAgentLinux.cpp | send_message             | [** <<SER>> **]        | client_key: 0x07DB5524, len: 14, data: 
0000: 81 01 02 00 05 01 06 00 00 25 00 03 00 00
[1669990948.882088] debug    | SerialAgentLinux.cpp | send_message             | [** <<SER>> **]        | client_key: 0x07DB5524, len: 14, data: 
0000: 81 01 03 00 05 01 06 00 00 26 00 12 00 00
[1669990948.882098] debug    | ProxyClient.cpp    | delete_object_unlock     | object deleted         | client_key: 0x07DB5524, object_id: 0x0001
[1669990948.882115] debug    | ProxyClient.cpp    | delete_object_unlock     | object deleted         | client_key: 0x07DB5524, object_id: 0x0001
[1669990948.882194] debug    | SerialAgentLinux.cpp | send_message             | [** <<SER>> **]        | client_key: 0x07DB5524, len: 14, data: 
0000: 81 01 04 00 05 01 06 00 00 27 00 15 00 00
[1669990948.882204] debug    | SerialAgentLinux.cpp | send_message             | [** <<SER>> **]        | client_key: 0x07DB5524, len: 14, data: 
0000: 81 01 05 00 05 01 06 00 00 28 00 13 00 00
[1669990948.882220] debug    | SerialAgentLinux.cpp | recv_message             | [==>> SER <<==]        | client_key: 0x07DB5524, len: 12, data: 
0000: 81 01 13 00 03 01 04 00 00 2A 00 22
[1669990948.882249] debug    | SerialAgentLinux.cpp | recv_message             | [==>> SER <<==]        | client_key: 0x07DB5524, len: 20, data: 
0000: 81 01 14 00 03 01 04 00 00 2B 00 06 03 01 04 00 00 2C 00 04
[1669990948.882255] debug    | SerialAgentLinux.cpp | recv_message             | [==>> SER <<==]        | client_key: 0x07DB5524, len: 12, data: 
0000: 81 01 15 00 03 01 04 00 00 2D 00 01
[1669990948.882410] debug    | SerialAgentLinux.cpp | recv_message             | [==>> SER <<==]        | client_key: 0x07DB5524, len: 12, data: 
0000: 81 00 00 00 03 01 04 00 00 02 FF FE
[1669990948.970260] debug    | ProxyClient.cpp    | delete_object_unlock     | object deleted         | client_key: 0x07DB5524, object_id: 0x0002
[1669990948.970360] debug    | SerialAgentLinux.cpp | send_message             | [** <<SER>> **]        | client_key: 0x07DB5524, len: 14, data: 
0000: 81 01 06 00 05 01 06 00 00 2A 00 22 00 00
[1669990949.001064] debug    | SerialAgentLinux.cpp | recv_message             | [==>> SER <<==]        | client_key: 0x07DB5524, len: 16, data: 
0000: 80 00 00 00 02 01 08 00 00 0A FF FD 02 00 00 00
[1669990949.070699] debug    | ProxyClient.cpp    | delete_object_unlock     | object deleted         | client_key: 0x07DB5524, object_id: 0x0000
[1669990949.070788] debug    | ProxyClient.cpp    | delete_object_unlock     | object deleted         | client_key: 0x07DB5524, object_id: 0x0000
[1669990949.070979] debug    | SerialAgentLinux.cpp | send_message             | [** <<SER>> **]        | client_key: 0x07DB5524, len: 14, data: 
0000: 81 01 07 00 05 01 06 00 00 2B 00 06 00 00
[1669990949.071001] debug    | SerialAgentLinux.cpp | send_message             | [** <<SER>> **]        | client_key: 0x07DB5524, len: 14, data: 
0000: 81 01 08 00 05 01 06 00 00 2C 00 04 00 00
[1669990949.074165] debug    | ProxyClient.cpp    | delete_object_unlock     | object deleted         | client_key: 0x07DB5524, object_id: 0x0000
[1669990949.074225] info     | Root.cpp           | delete_client            | delete                 | client_key: 0x07DB5524
[1669990949.074237] info     | SessionManager.hpp | destroy_session          | session closed         | client_key: 0x07DB5524, address: 0
[1669990949.090081] info     | Root.cpp           | create_client            | create                 | client_key: 0x7AB1124A, session_id: 0x81
[1669990949.090118] info     | SessionManager.hpp | establish_session        | session established    | client_key: 0x7AB1124A, address: 0
[1669990949.090178] debug    | SerialAgentLinux.cpp | send_message             | [** <<SER>> **]        | client_key: 0x7AB1124A, len: 19, data: 
0000: 81 00 00 00 04 01 0B 00 00 00 58 52 43 45 01 00 01 0F 00
[1669990949.093581] debug    | SerialAgentLinux.cpp | recv_message             | [==>> SER <<==]        | client_key: 0x7AB1124A, len: 48, data: 
0000: 81 80 00 00 01 07 28 00 00 0A 00 01 01 03 00 00 1A 00 00 00 00 01 FC 3F 12 00 00 00 74 69 61 6E
0020: 63 69 5F 72 6F 62 6F 74 5F 6E 6F 64 65 00 00 00
[1669990949.098195] info     | ProxyClient.cpp    | create_participant       | participant created    | client_key: 0x7AB1124A, participant_id: 0x000(1)
[1669990949.098493] debug    | SerialAgentLinux.cpp | send_message             | [** <<SER>> **]        | client_key: 0x7AB1124A, len: 14, data: 
0000: 81 80 00 00 05 01 06 00 00 0A 00 01 00 00
[1669990949.098514] debug    | SerialAgentLinux.cpp | send_message             | [** <<SER>> **]        | client_key: 0x7AB1124A, len: 13, data: 
0000: 81 00 00 00 0A 01 05 00 01 00 00 00 80
[1669990949.105314] debug    | SerialAgentLinux.cpp | recv_message             | [==>> SER <<==]        | client_key: 0x7AB1124A, len: 13, data: 
0000: 81 00 00 00 0A 01 05 00 01 00 00 00 80
[1669990949.105747] debug    | SerialAgentLinux.cpp | recv_message             | [==>> SER <<==]        | client_key: 0x7AB1124A, len: 88, data: 
0000: 81 80 01 00 01 07 4D 00 00 0B 00 02 02 03 00 00 3F 00 00 00 13 00 00 00 72 74 2F 6F 64 6F 6D 2F
0020: 75 6E 66 69 6C 74 65 72 65 64 00 00 01 95 FB 3F 1F 00 00 00 6E 61 76 5F 6D 73 67 73 3A 3A 6D 73
0040: 67 3A 3A 64 64 73 5F 3A 3A 4F 64 6F 6D 65 74 72 79 5F 00 00 01 00 00 00
[1669990949.105852] info     | ProxyClient.cpp    | create_topic             | topic created          | client_key: 0x7AB1124A, topic_id: 0x000(2), participant_id: 0x000(1)
[1669990949.106011] debug    | SerialAgentLinux.cpp | send_message             | [** <<SER>> **]        | client_key: 0x7AB1124A, len: 14, data: 
0000: 81 80 01 00 05 01 06 00 00 0B 00 02 00 00
[1669990949.106032] debug    | SerialAgentLinux.cpp | send_message             | [** <<SER>> **]        | client_key: 0x7AB1124A, len: 13, data: 
0000: 81 00 00 00 0A 01 05 00 02 00 00 00 80
[1669990949.110150] debug    | SerialAgentLinux.cpp | recv_message             | [==>> SER <<==]        | client_key: 0x7AB1124A, len: 13, data: 
0000: 81 00 00 00 0A 01 05 00 02 00 00 00 80
[1669990949.110189] debug    | SerialAgentLinux.cpp | recv_message             | [==>> SER <<==]        | client_key: 0x7AB1124A, len: 24, data: 
0000: 81 80 02 00 01 07 10 00 00 0C 00 03 03 03 00 01 02 00 00 00 00 00 00 01
[1669990949.110277] info     | ProxyClient.cpp    | create_publisher         | publisher created      | client_key: 0x7AB1124A, publisher_id: 0x000(3), participant_id: 0x000(1)
[1669990949.110386] debug    | SerialAgentLinux.cpp | send_message             | [** <<SER>> **]        | client_key: 0x7AB1124A, len: 14, data: 
0000: 81 80 02 00 05 01 06 00 00 0C 00 03 00 00
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
0120: 00 00 00 00 00 00 00 00 00 00 00 00 00 00 00 00 00 00 00 00 00 00 00 00 00 00 00 80 B5 F8 E4 3E
[1669990949.465060] debug    | SerialAgentLinux.cpp | recv_message             | [==>> SER <<==]        | client_key: 0x7AB1124A, len: 12, data: 
0000: 81 01 0E 00 03 01 04 00 00 23 00 02
[1669990949.465106] debug    | SerialAgentLinux.cpp | recv_message             | [==>> SER <<==]        | client_key: 0x7AB1124A, len: 20, data: 
0000: 81 01 0F 00 03 01 04 00 00 24 00 05 03 01 04 00 00 25 00 03
[1669990949.465117] debug    | SerialAgentLinux.cpp | recv_message             | [==>> SER <<==]        | client_key: 0x7AB1124A, len: 12, data: 
0000: 81 01 10 00 03 01 04 00 00 26 00 12
[1669990949.465156] debug    | ProxyClient.cpp    | delete_object_unlock     | object deleted         | client_key: 0x7AB1124A, object_id: 0x0000
[1669990949.465158] debug    | SerialAgentLinux.cpp | recv_message             | [==>> SER <<==]        | client_key: 0x7AB1124A, len: 20, data: 
0000: 81 01 11 00 03 01 04 00 00 27 00 15 03 01 04 00 00 28 00 13
[1669990949.465228] debug    | SerialAgentLinux.cpp | send_message             | [** <<SER>> **]        | client_key: 0x7AB1124A, len: 14, data: 
0000: 81 01 00 00 05 01 06 00 00 23 00 02 00 00
[1669990949.465230] debug    | SerialAgentLinux.cpp | recv_message             | [==>> SER <<==]        | client_key: 0x7AB1124A, len: 24, data: 
0000: 81 01 12 00 08 01 10 00 00 29 00 06 00 00 00 01 00 00 00 00 00 00 00 00
[1669990949.465444] debug    | SerialAgentLinux.cpp | recv_message             | [==>> SER <<==]        | client_key: 0x7AB1124A, len: 12, data: 
0000: 81 01 13 00 03 01 04 00 00 2A 00 22
[1669990949.465456] debug    | SerialAgentLinux.cpp | recv_message             | [==>> SER <<==]        | client_key: 0x7AB1124A, len: 20, data: 
0000: 81 01 14 00 03 01 04 00 00 2B 00 06 03 01 04 00 00 2C 00 04
[1669990949.465467] debug    | SerialAgentLinux.cpp | recv_message             | [==>> SER <<==]        | client_key: 0x7AB1124A, len: 12, data: 
0000: 81 01 15 00 03 01 04 00 00 2D 00 01
[1669990949.465478] debug    | SerialAgentLinux.cpp | recv_message             | [==>> SER <<==]        | client_key: 0x7AB1124A, len: 12, data: 
0000: 81 00 00 00 03 01 04 00 00 02 FF FE
[1669990949.465608] debug    | ProxyClient.cpp    | delete_object_unlock     | object deleted         | client_key: 0x7AB1124A, object_id: 0x0000
[1669990949.465640] debug    | ProxyClient.cpp    | delete_object_unlock     | object deleted         | client_key: 0x7AB1124A, object_id: 0x0000
[1669990949.465646] debug    | ProxyClient.cpp    | delete_object_unlock     | object deleted         | client_key: 0x7AB1124A, object_id: 0x0001
[1669990949.465666] debug    | SerialAgentLinux.cpp | send_message             | [** <<SER>> **]        | client_key: 0x7AB1124A, len: 14, data: 
0000: 81 01 01 00 05 01 06 00 00 24 00 05 00 00
[1669990949.465675] debug    | SerialAgentLinux.cpp | send_message             | [** <<SER>> **]        | client_key: 0x7AB1124A, len: 14, data: 
0000: 81 01 02 00 05 01 06 00 00 25 00 03 00 00
[1669990949.465679] debug    | SerialAgentLinux.cpp | send_message             | [** <<SER>> **]        | client_key: 0x7AB1124A, len: 14, data: 
0000: 81 01 03 00 05 01 06 00 00 26 00 12 00 00
[1669990949.465892] debug    | ProxyClient.cpp    | delete_object_unlock     | object deleted         | client_key: 0x7AB1124A, object_id: 0x0001
[1669990949.465921] debug    | ProxyClient.cpp    | delete_object_unlock     | object deleted         | client_key: 0x7AB1124A, object_id: 0x0001
[1669990949.465945] debug    | SerialAgentLinux.cpp | send_message             | [** <<SER>> **]        | client_key: 0x7AB1124A, len: 14, data: 
0000: 81 01 04 00 05 01 06 00 00 27 00 15 00 00
[1669990949.465961] debug    | SerialAgentLinux.cpp | send_message             | [** <<SER>> **]        | client_key: 0x7AB1124A, len: 14, data: 
0000: 81 01 05 00 05 01 06 00 00 28 00 13 00 00
[1669990949.549750] debug    | ProxyClient.cpp    | delete_object_unlock     | object deleted         | client_key: 0x7AB1124A, object_id: 0x0002
[1669990949.549942] debug    | SerialAgentLinux.cpp | send_message             | [** <<SER>> **]        | client_key: 0x7AB1124A, len: 14, data: 
0000: 81 01 06 00 05 01 06 00 00 2A 00 22 00 00
[1669990949.589901] debug    | SerialAgentLinux.cpp | recv_message             | [==>> SER <<==]        | client_key: 0x7AB1124A, len: 16, data: 
0000: 80 00 00 00 02 01 08 00 00 0A FF FD 02 00 00 00
[1669990949.650250] debug    | ProxyClient.cpp    | delete_object_unlock     | object deleted         | client_key: 0x7AB1124A, object_id: 0x0000
[1669990949.650314] debug    | ProxyClient.cpp    | delete_object_unlock     | object deleted         | client_key: 0x7AB1124A, object_id: 0x0000
[1669990949.650400] debug    | SerialAgentLinux.cpp | send_message             | [** <<SER>> **]        | client_key: 0x7AB1124A, len: 14, data: 
0000: 81 01 07 00 05 01 06 00 00 2B 00 06 00 00
[1669990949.650422] debug    | SerialAgentLinux.cpp | send_message             | [** <<SER>> **]        | client_key: 0x7AB1124A, len: 14, data: 
0000: 81 01 08 00 05 01 06 00 00 2C 00 04 00 00
[1669990949.653457] debug    | ProxyClient.cpp    | delete_object_unlock     | object deleted         | client_key: 0x7AB1124A, object_id: 0x0000
[1669990949.653524] info     | Root.cpp           | delete_client            | delete                 | client_key: 0x7AB1124A
[1669990949.653546] info     | SessionManager.hpp | destroy_session          | session closed         | client_key: 0x7AB1124A, address: 0
[1669990949.673265] info     | Root.cpp           | create_client            | create                 | client_key: 0x49342EC6, session_id: 0x81
[1669990949.673298] info     | SessionManager.hpp | establish_session        | session established    | client_key: 0x49342EC6, address: 0
[1669990949.673362] debug    | SerialAgentLinux.cpp | send_message             | [** <<SER>> **]        | client_key: 0x49342EC6, len: 19, data: 
0000: 81 00 00 00 04 01 0B 00 00 00 58 52 43 45 01 00 01 0F 00
[1669990949.677838] debug    | SerialAgentLinux.cpp | recv_message             | [==>> SER <<==]        | client_key: 0x49342EC6, len: 48, data: 
0000: 81 80 00 00 01 07 28 00 00 0A 00 01 01 03 00 00 1A 00 00 00 00 01 0F 80 12 00 00 00 74 69 61 6E
0020: 63 69 5F 72 6F 62 6F 74 5F 6E 6F 64 65 00 00 00
[1669990949.685573] info     | ProxyClient.cpp    | create_participant       | participant created    | client_key: 0x49342EC6, participant_id: 0x000(1)
[1669990949.685658] debug    | SerialAgentLinux.cpp | send_message             | [** <<SER>> **]        | client_key: 0x49342EC6, len: 14, data: 
0000: 81 80 00 00 05 01 06 00 00 0A 00 01 00 00
[1669990949.685683] debug    | SerialAgentLinux.cpp | send_message             | [** <<SER>> **]        | client_key: 0x49342EC6, len: 13, data: 
0000: 81 00 00 00 0A 01 05 00 01 00 00 00 80
[1669990949.690904] debug    | SerialAgentLinux.cpp | recv_message             | [==>> SER <<==]        | client_key: 0x49342EC6, len: 13, data: 
0000: 81 00 00 00 0A 01 05 00 01 00 00 00 80
[1669990949.693162] debug    | SerialAgentLinux.cpp | recv_message             | [==>> SER <<==]        | client_key: 0x49342EC6, len: 88, data: 
0000: 81 80 01 00 01 07 4D 00 00 0B 00 02 02 03 00 00 3F 00 00 00 13 00 00 00 72 74 2F 6F 64 6F 6D 2F
0020: 75 6E 66 69 6C 74 65 72 65 64 00 00 01 02 06 00 1F 00 00 00 6E 61 76 5F 6D 73 67 73 3A 3A 6D 73
0040: 67 3A 3A 64 64 73 5F 3A 3A 4F 64 6F 6D 65 74 72 79 5F 00 00 01 00 00 00
[1669990949.693268] info     | ProxyClient.cpp    | create_topic             | topic created          | client_key: 0x49342EC6, topic_id: 0x000(2), participant_id: 0x000(1)
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
0000: 81 01 03 00 05 01 06 00 00 26 00 12 00 00
[1669990950.062754] debug    | ProxyClient.cpp    | delete_object_unlock     | object deleted         | client_key: 0x49342EC6, object_id: 0x0001
[1669990950.062790] debug    | ProxyClient.cpp    | delete_object_unlock     | object deleted         | client_key: 0x49342EC6, object_id: 0x0001
[1669990950.062793] debug    | SerialAgentLinux.cpp | send_message             | [** <<SER>> **]        | client_key: 0x49342EC6, len: 14, data: 
0000: 81 01 04 00 05 01 06 00 00 27 00 15 00 00
[1669990950.062829] debug    | SerialAgentLinux.cpp | send_message             | [** <<SER>> **]        | client_key: 0x49342EC6, len: 14, data: 
0000: 81 01 05 00 05 01 06 00 00 28 00 13 00 00
[1669990950.062932] debug    | SerialAgentLinux.cpp | recv_message             | [==>> SER <<==]        | client_key: 0x49342EC6, len: 12, data: 
0000: 81 01 15 00 03 01 04 00 00 2D 00 01
[1669990950.065037] debug    | SerialAgentLinux.cpp | recv_message             | [==>> SER <<==]        | client_key: 0x49342EC6, len: 12, data: 
0000: 81 00 00 00 03 01 04 00 00 02 FF FE
[1669990950.157621] debug    | ProxyClient.cpp    | delete_object_unlock     | object deleted         | client_key: 0x49342EC6, object_id: 0x0000
[1669990950.157722] debug    | SerialAgentLinux.cpp | send_message             | [** <<SER>> **]        | client_key: 0x49342EC6, len: 14, data: 
0000: 81 01 06 00 05 01 06 00 00 2D 00 01 00 00
[1669990950.173211] debug    | SerialAgentLinux.cpp | recv_message             | [==>> SER <<==]        | client_key: 0x49342EC6, len: 16, data: 
0000: 80 00 00 00 02 01 08 00 00 0A FF FD 02 00 00 00
[1669990950.259127] info     | Root.cpp           | delete_client            | delete                 | client_key: 0x49342EC6
[1669990950.259163] info     | SessionManager.hpp | destroy_session          | session closed         | client_key: 0x49342EC6, address: 0
[1669990950.277265] info     | Root.cpp           | create_client            | create                 | client_key: 0x2644F3EA, session_id: 0x81
[1669990950.277327] info     | SessionManager.hpp | establish_session        | session established    | client_key: 0x2644F3EA, address: 0
[1669990950.277354] debug    | SerialAgentLinux.cpp | send_message             | [** <<SER>> **]        | client_key: 0x2644F3EA, len: 19, data: 
0000: 81 00 00 00 04 01 0B 00 00 00 58 52 43 45 01 00 01 0F 00
[1669990950.281369] debug    | SerialAgentLinux.cpp | recv_message             | [==>> SER <<==]        | client_key: 0x2644F3EA, len: 48, data: 
0000: 81 80 00 00 01 07 28 00 00 0A 00 01 01 03 00 00 1A 00 00 00 00 01 00 00 12 00 00 00 74 69 61 6E
0020: 63 69 5F 72 6F 62 6F 74 5F 6E 6F 64 65 00 00 00
[1669990950.286174] info     | ProxyClient.cpp    | create_participant       | participant created    | client_key: 0x2644F3EA, participant_id: 0x000(1)
[1669990950.286227] debug    | SerialAgentLinux.cpp | send_message             | [** <<SER>> **]        | client_key: 0x2644F3EA, len: 14, data: 
0000: 81 80 00 00 05 01 06 00 00 0A 00 01 00 00
[1669990950.286309] debug    | SerialAgentLinux.cpp | send_message             | [** <<SER>> **]        | client_key: 0x2644F3EA, len: 13, data: 
0000: 81 00 00 00 0A 01 05 00 01 00 00 00 80
[1669990950.293105] debug    | SerialAgentLinux.cpp | recv_message             | [==>> SER <<==]        | client_key: 0x2644F3EA, len: 13, data: 
0000: 81 00 00 00 0A 01 05 00 01 00 00 00 80
[1669990950.293246] debug    | SerialAgentLinux.cpp | recv_message             | [==>> SER <<==]        | client_key: 0x2644F3EA, len: 88, data: 
0000: 81 80 01 00 01 07 4D 00 00 0B 00 02 02 03 00 00 3F 00 00 00 13 00 00 00 72 74 2F 6F 64 6F 6D 2F
0020: 75 6E 66 69 6C 74 65 72 65 64 00 00 01 02 06 00 1F 00 00 00 6E 61 76 5F 6D 73 67 73 3A 3A 6D 73
0040: 67 3A 3A 64 64 73 5F 3A 3A 4F 64 6F 6D 65 74 72 79 5F 00 00 01 00 00 00
[1669990950.293324] info     | ProxyClient.cpp    | create_topic             | topic created          | client_key: 0x2644F3EA, topic_id: 0x000(2), participant_id: 0x000(1)
[1669990950.293358] debug    | SerialAgentLinux.cpp | send_message             | [** <<SER>> **]        | client_key: 0x2644F3EA, len: 14, data: 
0000: 81 80 01 00 05 01 06 00 00 0B 00 02 00 00
[1669990950.293368] debug    | SerialAgentLinux.cpp | send_message             | [** <<SER>> **]        | client_key: 0x2644F3EA, len: 13, data: 
0000: 81 00 00 00 0A 01 05 00 02 00 00 00 80
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
[1669990950.661272] debug    | SerialAgentLinux.cpp | send_message             | [** <<SER>> **]        | client_key: 0x2644F3EA, len: 14, data: 
0000: 81 01 00 00 05 01 06 00 00 23 00 02 00 00
[1669990950.661298] debug    | SerialAgentLinux.cpp | recv_message             | [==>> SER <<==]        | client_key: 0x2644F3EA, len: 24, data: 
0000: 81 01 12 00 08 01 10 00 00 29 00 06 00 00 00 01 00 00 00 00 00 00 00 00
[1669990950.661712] debug    | SerialAgentLinux.cpp | recv_message             | [==>> SER <<==]        | client_key: 0x2644F3EA, len: 12, data: 
0000: 81 01 13 00 03 01 04 00 00 2A 00 22
[1669990950.661860] debug    | ProxyClient.cpp    | delete_object_unlock     | object deleted         | client_key: 0x2644F3EA, object_id: 0x0000
[1669990950.661890] debug    | ProxyClient.cpp    | delete_object_unlock     | object deleted         | client_key: 0x2644F3EA, object_id: 0x0000
[1669990950.661944] debug    | ProxyClient.cpp    | delete_object_unlock     | object deleted         | client_key: 0x2644F3EA, object_id: 0x0001
[1669990950.661965] debug    | SerialAgentLinux.cpp | recv_message             | [==>> SER <<==]        | client_key: 0x2644F3EA, len: 20, data: 
0000: 81 01 14 00 03 01 04 00 00 2B 00 06 03 01 04 00 00 2C 00 04
[1669990950.661985] debug    | SerialAgentLinux.cpp | recv_message             | [==>> SER <<==]        | client_key: 0x2644F3EA, len: 12, data: 
0000: 81 01 15 00 03 01 04 00 00 2D 00 01
[1669990950.661911] debug    | SerialAgentLinux.cpp | send_message             | [** <<SER>> **]        | client_key: 0x2644F3EA, len: 14, data: 
0000: 81 01 01 00 05 01 06 00 00 24 00 05 00 00
[1669990950.662005] debug    | SerialAgentLinux.cpp | send_message             | [** <<SER>> **]        | client_key: 0x2644F3EA, len: 14, data: 
0000: 81 01 02 00 05 01 06 00 00 25 00 03 00 00
[1669990950.662013] debug    | SerialAgentLinux.cpp | send_message             | [** <<SER>> **]        | client_key: 0x2644F3EA, len: 14, data: 
0000: 81 01 03 00 05 01 06 00 00 26 00 12 00 00
[1669990950.662210] debug    | ProxyClient.cpp    | delete_object_unlock     | object deleted         | client_key: 0x2644F3EA, object_id: 0x0001
[1669990950.662231] debug    | ProxyClient.cpp    | delete_object_unlock     | object deleted         | client_key: 0x2644F3EA, object_id: 0x0001
[1669990950.662265] debug    | SerialAgentLinux.cpp | send_message             | [** <<SER>> **]        | client_key: 0x2644F3EA, len: 14, data: 
0000: 81 01 04 00 05 01 06 00 00 27 00 15 00 00
[1669990950.662286] debug    | SerialAgentLinux.cpp | send_message             | [** <<SER>> **]        | client_key: 0x2644F3EA, len: 14, data: 
0000: 81 01 05 00 05 01 06 00 00 28 00 13 00 00
[1669990950.662274] debug    | SerialAgentLinux.cpp | recv_message             | [==>> SER <<==]        | client_key: 0x2644F3EA, len: 12, data: 
0000: 81 00 00 00 03 01 04 00 00 02 FF FE
[1669990950.753111] debug    | ProxyClient.cpp    | delete_object_unlock     | object deleted         | client_key: 0x2644F3EA, object_id: 0x0002
[1669990950.753323] debug    | SerialAgentLinux.cpp | send_message             | [** <<SER>> **]        | client_key: 0x2644F3EA, len: 14, data: 
0000: 81 01 06 00 05 01 06 00 00 2A 00 22 00 00
[1669990950.777077] debug    | SerialAgentLinux.cpp | recv_message             | [==>> SER <<==]        | client_key: 0x2644F3EA, len: 16, data: 
0000: 80 00 00 00 02 01 08 00 00 0A FF FD 02 00 00 00
[1669990950.853512] debug    | ProxyClient.cpp    | delete_object_unlock     | object deleted         | client_key: 0x2644F3EA, object_id: 0x0000
[1669990950.853690] debug    | ProxyClient.cpp    | delete_object_unlock     | object deleted         | client_key: 0x2644F3EA, object_id: 0x0000
[1669990950.853777] debug    | SerialAgentLinux.cpp | send_message             | [** <<SER>> **]        | client_key: 0x2644F3EA, len: 14, data: 
0000: 81 01 07 00 05 01 06 00 00 2B 00 06 00 00
[1669990950.853807] debug    | SerialAgentLinux.cpp | send_message             | [** <<SER>> **]        | client_key: 0x2644F3EA, len: 14, data: 
0000: 81 01 08 00 05 01 06 00 00 2C 00 04 00 00
[1669990950.854963] debug    | ProxyClient.cpp    | delete_object_unlock     | object deleted         | client_key: 0x2644F3EA, object_id: 0x0000
[1669990950.855027] info     | Root.cpp           | delete_client            | delete                 | client_key: 0x2644F3EA
[1669990950.855039] info     | SessionManager.hpp | destroy_session          | session closed         | client_key: 0x2644F3EA, address: 0
[1669990950.877211] info     | Root.cpp           | create_client            | create                 | client_key: 0x42940F26, session_id: 0x81
[1669990950.877248] info     | SessionManager.hpp | establish_session        | session established    | client_key: 0x42940F26, address: 0
[1669990950.877344] debug    | SerialAgentLinux.cpp | send_message             | [** <<SER>> **]        | client_key: 0x42940F26, len: 19, data: 
0000: 81 00 00 00 04 01 0B 00 00 00 58 52 43 45 01 00 01 0F 00
[1669990950.881137] debug    | SerialAgentLinux.cpp | recv_message             | [==>> SER <<==]        | client_key: 0x42940F26, len: 48, data: 
0000: 81 80 00 00 01 07 28 00 00 0A 00 01 01 03 00 00 1A 00 00 00 00 01 0F 80 12 00 00 00 74 69 61 6E
0020: 63 69 5F 72 6F 62 6F 74 5F 6E 6F 64 65 00 00 00
[1669990950.885219] info     | ProxyClient.cpp    | create_participant       | participant created    | client_key: 0x42940F26, participant_id: 0x000(1)
[1669990950.886368] debug    | SerialAgentLinux.cpp | send_message             | [** <<SER>> **]        | client_key: 0x42940F26, len: 14, data: 
0000: 81 80 00 00 05 01 06 00 00 0A 00 01 00 00
[1669990950.886440] debug    | SerialAgentLinux.cpp | send_message             | [** <<SER>> **]        | client_key: 0x42940F26, len: 13, data: 
0000: 81 00 00 00 0A 01 05 00 01 00 00 00 80
[1669990950.889350] debug    | SerialAgentLinux.cpp | recv_message             | [==>> SER <<==]        | client_key: 0x42940F26, len: 13, data: 
0000: 81 00 00 00 0A 01 05 00 01 00 00 00 80
[1669990950.893188] debug    | SerialAgentLinux.cpp | recv_message             | [==>> SER <<==]        | client_key: 0x42940F26, len: 88, data: 
0000: 81 80 01 00 01 07 4D 00 00 0B 00 02 02 03 00 00 3F 00 00 00 13 00 00 00 72 74 2F 6F 64 6F 6D 2F
0020: 75 6E 66 69 6C 74 65 72 65 64 00 00 01 31 FC 3F 1F 00 00 00 6E 61 76 5F 6D 73 67 73 3A 3A 6D 73
0040: 67 3A 3A 64 64 73 5F 3A 3A 4F 64 6F 6D 65 74 72 79 5F 00 00 01 00 00 00
[1669990950.893412] info     | ProxyClient.cpp    | create_topic             | topic created          | client_key: 0x42940F26, topic_id: 0x000(2), participant_id: 0x000(1)
[1669990950.893473] debug    | SerialAgentLinux.cpp | send_message             | [** <<SER>> **]        | client_key: 0x42940F26, len: 14, data: 
0000: 81 80 01 00 05 01 06 00 00 0B 00 02 00 00
[1669990950.893489] debug    | SerialAgentLinux.cpp | send_message             | [** <<SER>> **]        | client_key: 0x42940F26, len: 13, data: 
0000: 81 00 00 00 0A 01 05 00 02 00 00 00 80
[1669990950.897144] debug    | SerialAgentLinux.cpp | recv_message             | [==>> SER <<==]        | client_key: 0x42940F26, len: 13, data: 
0000: 81 00 00 00 0A 01 05 00 02 00 00 00 80
[1669990950.897240] debug    | SerialAgentLinux.cpp | recv_message             | [==>> SER <<==]        | client_key: 0x42940F26, len: 24, data: 
0000: 81 80 02 00 01 07 10 00 00 0C 00 03 03 03 00 01 02 00 00 00 00 00 00 01
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
[1669990951.261683] debug    | ProxyClient.cpp    | delete_object_unlock     | object deleted         | client_key: 0x42940F26, object_id: 0x0000
[1669990951.261713] debug    | ProxyClient.cpp    | delete_object_unlock     | object deleted         | client_key: 0x42940F26, object_id: 0x0000
[1669990951.261719] debug    | ProxyClient.cpp    | delete_object_unlock     | object deleted         | client_key: 0x42940F26, object_id: 0x0001
[1669990951.261750] debug    | SerialAgentLinux.cpp | recv_message             | [==>> SER <<==]        | client_key: 0x42940F26, len: 12, data: 
0000: 81 01 13 00 03 01 04 00 00 2A 00 22
[1669990951.261861] debug    | SerialAgentLinux.cpp | send_message             | [** <<SER>> **]        | client_key: 0x42940F26, len: 14, data: 
0000: 81 01 01 00 05 01 06 00 00 24 00 05 00 00
[1669990951.261904] debug    | SerialAgentLinux.cpp | send_message             | [** <<SER>> **]        | client_key: 0x42940F26, len: 14, data: 
0000: 81 01 02 00 05 01 06 00 00 25 00 03 00 00
[1669990951.261914] debug    | SerialAgentLinux.cpp | send_message             | [** <<SER>> **]        | client_key: 0x42940F26, len: 14, data: 
0000: 81 01 03 00 05 01 06 00 00 26 00 12 00 00
[1669990951.262089] debug    | ProxyClient.cpp    | delete_object_unlock     | object deleted         | client_key: 0x42940F26, object_id: 0x0001
[1669990951.262179] debug    | ProxyClient.cpp    | delete_object_unlock     | object deleted         | client_key: 0x42940F26, object_id: 0x0001
[1669990951.262198] debug    | SerialAgentLinux.cpp | recv_message             | [==>> SER <<==]        | client_key: 0x42940F26, len: 20, data: 
0000: 81 01 14 00 03 01 04 00 00 2B 00 06 03 01 04 00 00 2C 00 04
[1669990951.262204] debug    | SerialAgentLinux.cpp | recv_message             | [==>> SER <<==]        | client_key: 0x42940F26, len: 12, data: 
0000: 81 01 15 00 03 01 04 00 00 2D 00 01
[1669990951.262211] debug    | SerialAgentLinux.cpp | recv_message             | [==>> SER <<==]        | client_key: 0x42940F26, len: 12, data: 
0000: 81 00 00 00 03 01 04 00 00 02 FF FE
[1669990951.262214] debug    | SerialAgentLinux.cpp | send_message             | [** <<SER>> **]        | client_key: 0x42940F26, len: 14, data: 
0000: 81 01 04 00 05 01 06 00 00 27 00 15 00 00
[1669990951.262297] debug    | SerialAgentLinux.cpp | send_message             | [** <<SER>> **]        | client_key: 0x42940F26, len: 14, data: 
0000: 81 01 05 00 05 01 06 00 00 28 00 13 00 00
[1669990951.357187] debug    | ProxyClient.cpp    | delete_object_unlock     | object deleted         | client_key: 0x42940F26, object_id: 0x0002
[1669990951.357278] debug    | SerialAgentLinux.cpp | send_message             | [** <<SER>> **]        | client_key: 0x42940F26, len: 14, data: 
0000: 81 01 06 00 05 01 06 00 00 2A 00 22 00 00
[1669990951.377089] debug    | SerialAgentLinux.cpp | recv_message             | [==>> SER <<==]        | client_key: 0x42940F26, len: 16, data: 
0000: 80 00 00 00 02 01 08 00 00 0A FF FD 02 00 00 00
[1669990951.457680] debug    | ProxyClient.cpp    | delete_object_unlock     | object deleted         | client_key: 0x42940F26, object_id: 0x0000
[1669990951.457731] debug    | ProxyClient.cpp    | delete_object_unlock     | object deleted         | client_key: 0x42940F26, object_id: 0x0000
[1669990951.457784] debug    | SerialAgentLinux.cpp | send_message             | [** <<SER>> **]        | client_key: 0x42940F26, len: 14, data: 
0000: 81 01 07 00 05 01 06 00 00 2B 00 06 00 00
[1669990951.457795] debug    | SerialAgentLinux.cpp | send_message             | [** <<SER>> **]        | client_key: 0x42940F26, len: 14, data: 
0000: 81 01 08 00 05 01 06 00 00 2C 00 04 00 00
[1669990951.458992] debug    | ProxyClient.cpp    | delete_object_unlock     | object deleted         | client_key: 0x42940F26, object_id: 0x0000
[1669990951.459055] info     | Root.cpp           | delete_client            | delete                 | client_key: 0x42940F26
[1669990951.459064] info     | SessionManager.hpp | destroy_session          | session closed         | client_key: 0x42940F26, address: 0
[1669990951.477165] info     | Root.cpp           | create_client            | create                 | client_key: 0x5BD97C26, session_id: 0x81
[1669990951.477190] info     | SessionManager.hpp | establish_session        | session established    | client_key: 0x5BD97C26, address: 0
[1669990951.477415] debug    | SerialAgentLinux.cpp | send_message             | [** <<SER>> **]        | client_key: 0x5BD97C26, len: 19, data: 
0000: 81 00 00 00 04 01 0B 00 00 00 58 52 43 45 01 00 01 0F 00
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
0000: 81 01 11 00 03 01 04 00 00 27 00 15 03 01 04 00 00 28 00 13
[1669990951.854220] debug    | SerialAgentLinux.cpp | recv_message             | [==>> SER <<==]        | client_key: 0x5BD97C26, len: 24, data: 
0000: 81 01 12 00 08 01 10 00 00 29 00 06 00 00 00 01 00 00 00 00 00 00 00 00
[1669990951.854460] debug    | ProxyClient.cpp    | delete_object_unlock     | object deleted         | client_key: 0x5BD97C26, object_id: 0x0000
[1669990951.854491] debug    | SerialAgentLinux.cpp | send_message             | [** <<SER>> **]        | client_key: 0x5BD97C26, len: 14, data: 
0000: 81 01 01 00 05 01 06 00 00 24 00 05 00 00
[1669990951.854501] debug    | ProxyClient.cpp    | delete_object_unlock     | object deleted         | client_key: 0x5BD97C26, object_id: 0x0000
[1669990951.854510] debug    | SerialAgentLinux.cpp | send_message             | [** <<SER>> **]        | client_key: 0x5BD97C26, len: 14, data: 
0000: 81 01 02 00 05 01 06 00 00 25 00 03 00 00
[1669990951.854517] debug    | ProxyClient.cpp    | delete_object_unlock     | object deleted         | client_key: 0x5BD97C26, object_id: 0x0001
[1669990951.854566] debug    | SerialAgentLinux.cpp | send_message             | [** <<SER>> **]        | client_key: 0x5BD97C26, len: 14, data: 
0000: 81 01 03 00 05 01 06 00 00 26 00 12 00 00
[1669990951.854652] debug    | SerialAgentLinux.cpp | recv_message             | [==>> SER <<==]        | client_key: 0x5BD97C26, len: 12, data: 
0000: 81 01 13 00 03 01 04 00 00 2A 00 22
[1669990951.854954] debug    | ProxyClient.cpp    | delete_object_unlock     | object deleted         | client_key: 0x5BD97C26, object_id: 0x0001
[1669990951.854973] debug    | SerialAgentLinux.cpp | send_message             | [** <<SER>> **]        | client_key: 0x5BD97C26, len: 14, data: 
0000: 81 01 04 00 05 01 06 00 00 27 00 15 00 00
[1669990951.854980] debug    | ProxyClient.cpp    | delete_object_unlock     | object deleted         | client_key: 0x5BD97C26, object_id: 0x0001
[1669990951.854989] debug    | SerialAgentLinux.cpp | send_message             | [** <<SER>> **]        | client_key: 0x5BD97C26, len: 14, data: 
0000: 81 01 05 00 05 01 06 00 00 28 00 13 00 00
[1669990951.857158] debug    | SerialAgentLinux.cpp | recv_message             | [==>> SER <<==]        | client_key: 0x5BD97C26, len: 20, data: 
0000: 81 01 14 00 03 01 04 00 00 2B 00 06 03 01 04 00 00 2C 00 04
[1669990951.857176] debug    | SerialAgentLinux.cpp | recv_message             | [==>> SER <<==]        | client_key: 0x5BD97C26, len: 12, data: 
0000: 81 01 15 00 03 01 04 00 00 2D 00 01
[1669990951.857182] debug    | SerialAgentLinux.cpp | recv_message             | [==>> SER <<==]        | client_key: 0x5BD97C26, len: 12, data: 
0000: 81 00 00 00 03 01 04 00 00 02 FF FE
[1669990951.941731] debug    | ProxyClient.cpp    | delete_object_unlock     | object deleted         | client_key: 0x5BD97C26, object_id: 0x0002
[1669990951.941811] debug    | SerialAgentLinux.cpp | send_message             | [** <<SER>> **]        | client_key: 0x5BD97C26, len: 14, data: 
0000: 81 01 06 00 05 01 06 00 00 2A 00 22 00 00
[1669990951.977224] debug    | SerialAgentLinux.cpp | recv_message             | [==>> SER <<==]        | client_key: 0x5BD97C26, len: 16, data: 
0000: 80 00 00 00 02 01 08 00 00 0A FF FD 02 00 00 00
[1669990952.042225] debug    | ProxyClient.cpp    | delete_object_unlock     | object deleted         | client_key: 0x5BD97C26, object_id: 0x0000
[1669990952.042335] debug    | SerialAgentLinux.cpp | send_message             | [** <<SER>> **]        | client_key: 0x5BD97C26, len: 14, data: 
0000: 81 01 07 00 05 01 06 00 00 2B 00 06 00 00
[1669990952.042359] debug    | ProxyClient.cpp    | delete_object_unlock     | object deleted         | client_key: 0x5BD97C26, object_id: 0x0000
[1669990952.042381] debug    | SerialAgentLinux.cpp | send_message             | [** <<SER>> **]        | client_key: 0x5BD97C26, len: 14, data: 
0000: 81 01 08 00 05 01 06 00 00 2C 00 04 00 00
[1669990952.050170] debug    | ProxyClient.cpp    | delete_object_unlock     | object deleted         | client_key: 0x5BD97C26, object_id: 0x0000
[1669990952.050275] debug    | SerialAgentLinux.cpp | send_message             | [** <<SER>> **]        | client_key: 0x5BD97C26, len: 14, data: 
0000: 81 01 09 00 05 01 06 00 00 2D 00 01 00 00
[1669990952.050304] info     | Root.cpp           | delete_client            | delete                 | client_key: 0x5BD97C26
[1669990952.050314] info     | SessionManager.hpp | destroy_session          | session closed         | client_key: 0x5BD97C26, address: 0
[1669990952.065836] info     | Root.cpp           | create_client            | create                 | client_key: 0x47061170, session_id: 0x81
[1669990952.065868] info     | SessionManager.hpp | establish_session        | session established    | client_key: 0x47061170, address: 0
[1669990952.065900] debug    | SerialAgentLinux.cpp | send_message             | [** <<SER>> **]        | client_key: 0x47061170, len: 19, data: 
0000: 81 00 00 00 04 01 0B 00 00 00 58 52 43 45 01 00 01 0F 00
[1669990952.070412] debug    | SerialAgentLinux.cpp | recv_message             | [==>> SER <<==]        | client_key: 0x47061170, len: 48, data: 
0000: 81 80 00 00 01 07 28 00 00 0A 00 01 01 03 00 00 1A 00 00 00 00 01 00 00 12 00 00 00 74 69 61 6E
0020: 63 69 5F 72 6F 62 6F 74 5F 6E 6F 64 65 00 00 00
[1669990952.077872] info     | ProxyClient.cpp    | create_participant       | participant created    | client_key: 0x47061170, participant_id: 0x000(1)
[1669990952.077932] debug    | SerialAgentLinux.cpp | send_message             | [** <<SER>> **]        | client_key: 0x47061170, len: 14, data: 
0000: 81 80 00 00 05 01 06 00 00 0A 00 01 00 00
[1669990952.077955] debug    | SerialAgentLinux.cpp | send_message             | [** <<SER>> **]        | client_key: 0x47061170, len: 13, data: 
0000: 81 00 00 00 0A 01 05 00 01 00 00 00 80
[1669990952.085109] debug    | SerialAgentLinux.cpp | recv_message             | [==>> SER <<==]        | client_key: 0x47061170, len: 13, data: 
0000: 81 00 00 00 0A 01 05 00 01 00 00 00 80
[1669990952.085147] debug    | SerialAgentLinux.cpp | recv_message             | [==>> SER <<==]        | client_key: 0x47061170, len: 88, data: 
0000: 81 80 01 00 01 07 4D 00 00 0B 00 02 02 03 00 00 3F 00 00 00 13 00 00 00 72 74 2F 6F 64 6F 6D 2F
0020: 75 6E 66 69 6C 74 65 72 65 64 00 00 01 59 FC 3F 1F 00 00 00 6E 61 76 5F 6D 73 67 73 3A 3A 6D 73
0040: 67 3A 3A 64 64 73 5F 3A 3A 4F 64 6F 6D 65 74 72 79 5F 00 00 01 00 00 00
[1669990952.085275] info     | ProxyClient.cpp    | create_topic             | topic created          | client_key: 0x47061170, topic_id: 0x000(2), participant_id: 0x000(1)
[1669990952.085316] debug    | SerialAgentLinux.cpp | send_message             | [** <<SER>> **]        | client_key: 0x47061170, len: 14, data: 
0000: 81 80 01 00 05 01 06 00 00 0B 00 02 00 00
[1669990952.085337] debug    | SerialAgentLinux.cpp | send_message             | [** <<SER>> **]        | client_key: 0x47061170, len: 13, data: 
0000: 81 00 00 00 0A 01 05 00 02 00 00 00 80
[1669990952.089101] debug    | SerialAgentLinux.cpp | recv_message             | [==>> SER <<==]        | client_key: 0x47061170, len: 13, data: 
0000: 81 00 00 00 0A 01 05 00 02 00 00 00 80
[1669990952.089204] debug    | SerialAgentLinux.cpp | recv_message             | [==>> SER <<==]        | client_key: 0x47061170, len: 24, data: 
0000: 81 80 02 00 01 07 10 00 00 0C 00 03 03 03 00 01 02 00 00 00 00 00 00 01
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
0000: 81 01 4B 00 03 01 04 00 00 61 00 12
[1669990953.293190] debug    | SerialAgentLinux.cpp | recv_message             | [==>> SER <<==]        | client_key: 0x47061170, len: 20, data: 
0000: 81 01 4C 00 03 01 04 00 00 62 00 15 03 01 04 00 00 63 00 13
[1669990953.293201] debug    | SerialAgentLinux.cpp | recv_message             | [==>> SER <<==]        | client_key: 0x47061170, len: 24, data: 
0000: 81 01 4D 00 08 01 10 00 00 64 00 06 00 00 00 01 00 00 00 00 00 00 00 00
[1669990953.293298] debug    | ProxyClient.cpp    | delete_object_unlock     | object deleted         | client_key: 0x47061170, object_id: 0x0000
[1669990953.293468] debug    | SerialAgentLinux.cpp | send_message             | [** <<SER>> **]        | client_key: 0x47061170, len: 14, data: 
0000: 81 01 00 00 05 01 06 00 00 5E 00 02 00 00
[1669990953.293495] debug    | SerialAgentLinux.cpp | recv_message             | [==>> SER <<==]        | client_key: 0x47061170, len: 12, data: 
0000: 81 01 4E 00 03 01 04 00 00 65 00 22
[1669990953.293723] debug    | ProxyClient.cpp    | delete_object_unlock     | object deleted         | client_key: 0x47061170, object_id: 0x0000
[1669990953.293744] debug    | ProxyClient.cpp    | delete_object_unlock     | object deleted         | client_key: 0x47061170, object_id: 0x0000
[1669990953.293750] debug    | ProxyClient.cpp    | delete_object_unlock     | object deleted         | client_key: 0x47061170, object_id: 0x0001
[1669990953.293798] debug    | ProxyClient.cpp    | delete_object_unlock     | object deleted         | client_key: 0x47061170, object_id: 0x0001
[1669990953.293805] debug    | ProxyClient.cpp    | delete_object_unlock     | object deleted         | client_key: 0x47061170, object_id: 0x0001
[1669990953.293819] debug    | SerialAgentLinux.cpp | send_message             | [** <<SER>> **]        | client_key: 0x47061170, len: 14, data: 
0000: 81 01 01 00 05 01 06 00 00 5F 00 05 00 00
[1669990953.293824] debug    | SerialAgentLinux.cpp | send_message             | [** <<SER>> **]        | client_key: 0x47061170, len: 14, data: 
0000: 81 01 02 00 05 01 06 00 00 60 00 03 00 00
[1669990953.293846] debug    | SerialAgentLinux.cpp | send_message             | [** <<SER>> **]        | client_key: 0x47061170, len: 14, data: 
0000: 81 01 03 00 05 01 06 00 00 61 00 12 00 00
[1669990953.293851] debug    | SerialAgentLinux.cpp | send_message             | [** <<SER>> **]        | client_key: 0x47061170, len: 14, data: 
0000: 81 01 04 00 05 01 06 00 00 62 00 15 00 00
[1669990953.293894] debug    | SerialAgentLinux.cpp | send_message             | [** <<SER>> **]        | client_key: 0x47061170, len: 14, data: 
0000: 81 01 05 00 05 01 06 00 00 63 00 13 00 00
[1669990953.294020] debug    | SerialAgentLinux.cpp | recv_message             | [==>> SER <<==]        | client_key: 0x47061170, len: 20, data: 
0000: 81 01 4F 00 03 01 04 00 00 66 00 06 03 01 04 00 00 67 00 04
[1669990953.294043] debug    | SerialAgentLinux.cpp | recv_message             | [==>> SER <<==]        | client_key: 0x47061170, len: 12, data: 
0000: 81 01 50 00 03 01 04 00 00 68 00 01
[1669990953.294219] debug    | SerialAgentLinux.cpp | recv_message             | [==>> SER <<==]        | client_key: 0x47061170, len: 12, data: 
0000: 81 00 00 00 03 01 04 00 00 02 FF FE
[1669990953.305544] debug    | SerialAgentLinux.cpp | recv_message             | [==>> SER <<==]        | client_key: 0x47061170, len: 16, data: 
0000: 80 00 00 00 02 01 08 00 00 0A FF FD 02 00 00 00
[1669990953.345793] debug    | ProxyClient.cpp    | delete_object_unlock     | object deleted         | client_key: 0x47061170, object_id: 0x0002
[1669990953.345869] debug    | SerialAgentLinux.cpp | send_message             | [** <<SER>> **]        | client_key: 0x47061170, len: 14, data: 
0000: 81 01 06 00 05 01 06 00 00 65 00 22 00 00
[1669990953.446209] debug    | ProxyClient.cpp    | delete_object_unlock     | object deleted         | client_key: 0x47061170, object_id: 0x0000
[1669990953.446289] debug    | ProxyClient.cpp    | delete_object_unlock     | object deleted         | client_key: 0x47061170, object_id: 0x0000
[1669990953.446370] debug    | SerialAgentLinux.cpp | send_message             | [** <<SER>> **]        | client_key: 0x47061170, len: 14, data: 
0000: 81 01 07 00 05 01 06 00 00 66 00 06 00 00
[1669990953.446385] debug    | SerialAgentLinux.cpp | send_message             | [** <<SER>> **]        | client_key: 0x47061170, len: 14, data: 
0000: 81 01 08 00 05 01 06 00 00 67 00 04 00 00
[1669990953.454476] debug    | ProxyClient.cpp    | delete_object_unlock     | object deleted         | client_key: 0x47061170, object_id: 0x0000
[1669990953.454605] info     | Root.cpp           | delete_client            | delete                 | client_key: 0x47061170
[1669990953.454623] info     | SessionManager.hpp | destroy_session          | session closed         | client_key: 0x47061170, address: 0
[1669990953.973145] info     | Root.cpp           | create_client            | create                 | client_key: 0x4563E615, session_id: 0x81
[1669990953.973177] info     | SessionManager.hpp | establish_session        | session established    | client_key: 0x4563E615, address: 0
[1669990953.973202] debug    | SerialAgentLinux.cpp | send_message             | [** <<SER>> **]        | client_key: 0x4563E615, len: 19, data: 
0000: 81 00 00 00 04 01 0B 00 00 00 58 52 43 45 01 00 01 0F 00
[1669990953.977741] debug    | SerialAgentLinux.cpp | recv_message             | [==>> SER <<==]        | client_key: 0x4563E615, len: 48, data: 
0000: 81 80 00 00 01 07 28 00 00 0A 00 01 01 03 00 00 1A 00 00 00 00 01 00 00 12 00 00 00 74 69 61 6E
0020: 63 69 5F 72 6F 62 6F 74 5F 6E 6F 64 65 00 00 00
[1669990953.985167] info     | ProxyClient.cpp    | create_participant       | participant created    | client_key: 0x4563E615, participant_id: 0x000(1)
[1669990953.985210] debug    | SerialAgentLinux.cpp | send_message             | [** <<SER>> **]        | client_key: 0x4563E615, len: 14, data: 
0000: 81 80 00 00 05 01 06 00 00 0A 00 01 00 00
[1669990953.985237] debug    | SerialAgentLinux.cpp | send_message             | [** <<SER>> **]        | client_key: 0x4563E615, len: 13, data: 
0000: 81 00 00 00 0A 01 05 00 01 00 00 00 80
[1669990953.990352] debug    | SerialAgentLinux.cpp | recv_message             | [==>> SER <<==]        | client_key: 0x4563E615, len: 13, data: 
0000: 81 00 00 00 0A 01 05 00 01 00 00 00 80
[1669990953.990873] debug    | SerialAgentLinux.cpp | recv_message             | [==>> SER <<==]        | client_key: 0x4563E615, len: 88, data: 
0000: 81 80 01 00 01 07 4D 00 00 0B 00 02 02 03 00 00 3F 00 00 00 13 00 00 00 72 74 2F 6F 64 6F 6D 2F
0020: 75 6E 66 69 6C 74 65 72 65 64 00 00 01 95 FB 3F 1F 00 00 00 6E 61 76 5F 6D 73 67 73 3A 3A 6D 73
0040: 67 3A 3A 64 64 73 5F 3A 3A 4F 64 6F 6D 65 74 72 79 5F 00 00 01 00 00 00
[1669990953.990967] info     | ProxyClient.cpp    | create_topic             | topic created          | client_key: 0x4563E615, topic_id: 0x000(2), participant_id: 0x000(1)
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
