z2010012286/Robot_car/codes/reconfig_code/test_mpu9250_arduinoIDE/main/imu_interface.h

/*
 * @Author: Tianci Zhang
 * @Email: tianci_zhang@tju.edu.cn
 * @Date: 2022-11-15 17:25:02
 * @LastEditors: Tianci Zhang
 * @LastEditTime: 2022-11-16 14:19:52
 * @FilePath: \test_mpu9250\lib\imu\imu_interface.h
 * @Description: 
 * 
 * Copyright (c) 2022 by Tianci Zhang, All Rights Reserved. 
 */

#ifndef IMU_INTERFACE
#define IMU_INTERFACE

#include <sensor_msgs/msg/imu.h>

// #include <micro_ros_arduino.h>

class IMUInterface
{
    protected:
        sensor_msgs__msg__Imu imu_msg_;
        const float g_to_accel_ = 9.81;
        const float mgauss_to_utesla_ = 0.1;
        const float utesla_to_tesla_ = 0.000001;

        float accel_cov_ = 0.00001;
        float gyro_cov_ = 0.00001;
        const int sample_size_ = 40;

        geometry_msgs__msg__Vector3 gyro_cal_;

        void calibrateGyro()
        {
            geometry_msgs__msg__Vector3 gyro;

            for(int i=0; i<sample_size_; i++)
            {
                gyro = readGyroscope();
                gyro_cal_.x += gyro.x;
                gyro_cal_.y += gyro.y;
                gyro_cal_.z += gyro.z;

                delay(50);
            }

            gyro_cal_.x = gyro_cal_.x / (float)sample_size_;
            gyro_cal_.y = gyro_cal_.y / (float)sample_size_;
            gyro_cal_.z = gyro_cal_.z / (float)sample_size_;
        }
   
    public:
        IMUInterface()
        {
            // imu_msg_.header.frame_id = micro_ros_string_utilities_set(imu_msg_.header.frame_id, "imu_link"); //micro_ros foxy版本不可用，高版本可用
            imu_msg_.header.frame_id.data="imu_link";  //使用该语句代替。编译有warning，建议后续使用高版本micro_ros
        }

        virtual geometry_msgs__msg__Vector3 readAccelerometer() = 0;
        virtual geometry_msgs__msg__Vector3 readGyroscope() = 0;
        virtual bool startSensor() = 0;

        bool init()
        {
            bool sensor_ok = startSensor();
            if(sensor_ok)
                calibrateGyro();

            return sensor_ok;
        }

        sensor_msgs__msg__Imu getData()
        {
            imu_msg_.angular_velocity = readGyroscope();
            imu_msg_.angular_velocity.x -= gyro_cal_.x; 
            imu_msg_.angular_velocity.y -= gyro_cal_.y; 
            imu_msg_.angular_velocity.z -= gyro_cal_.z; 

            if(imu_msg_.angular_velocity.x > -0.01 && imu_msg_.angular_velocity.x < 0.01 )
                imu_msg_.angular_velocity.x = 0; 
         
            if(imu_msg_.angular_velocity.y > -0.01 && imu_msg_.angular_velocity.y < 0.01 )
                imu_msg_.angular_velocity.y = 0;

            if(imu_msg_.angular_velocity.z > -0.01 && imu_msg_.angular_velocity.z < 0.01 )
                imu_msg_.angular_velocity.z = 0;
       
            imu_msg_.angular_velocity_covariance[0] = gyro_cov_;
            imu_msg_.angular_velocity_covariance[4] = gyro_cov_;
            imu_msg_.angular_velocity_covariance[8] = gyro_cov_;
            
            imu_msg_.linear_acceleration = readAccelerometer();
            imu_msg_.linear_acceleration_covariance[0] = accel_cov_;
            imu_msg_.linear_acceleration_covariance[4] = accel_cov_;
            imu_msg_.linear_acceleration_covariance[8] = accel_cov_;

            return imu_msg_;
        }
};

#endif
